drandyhaas/HaasoscopePro/adc board/Kicad/ADC.kicad_sch

## KiCad design adc board/Kicad/ADC.kicad_sch (2025-04-30)

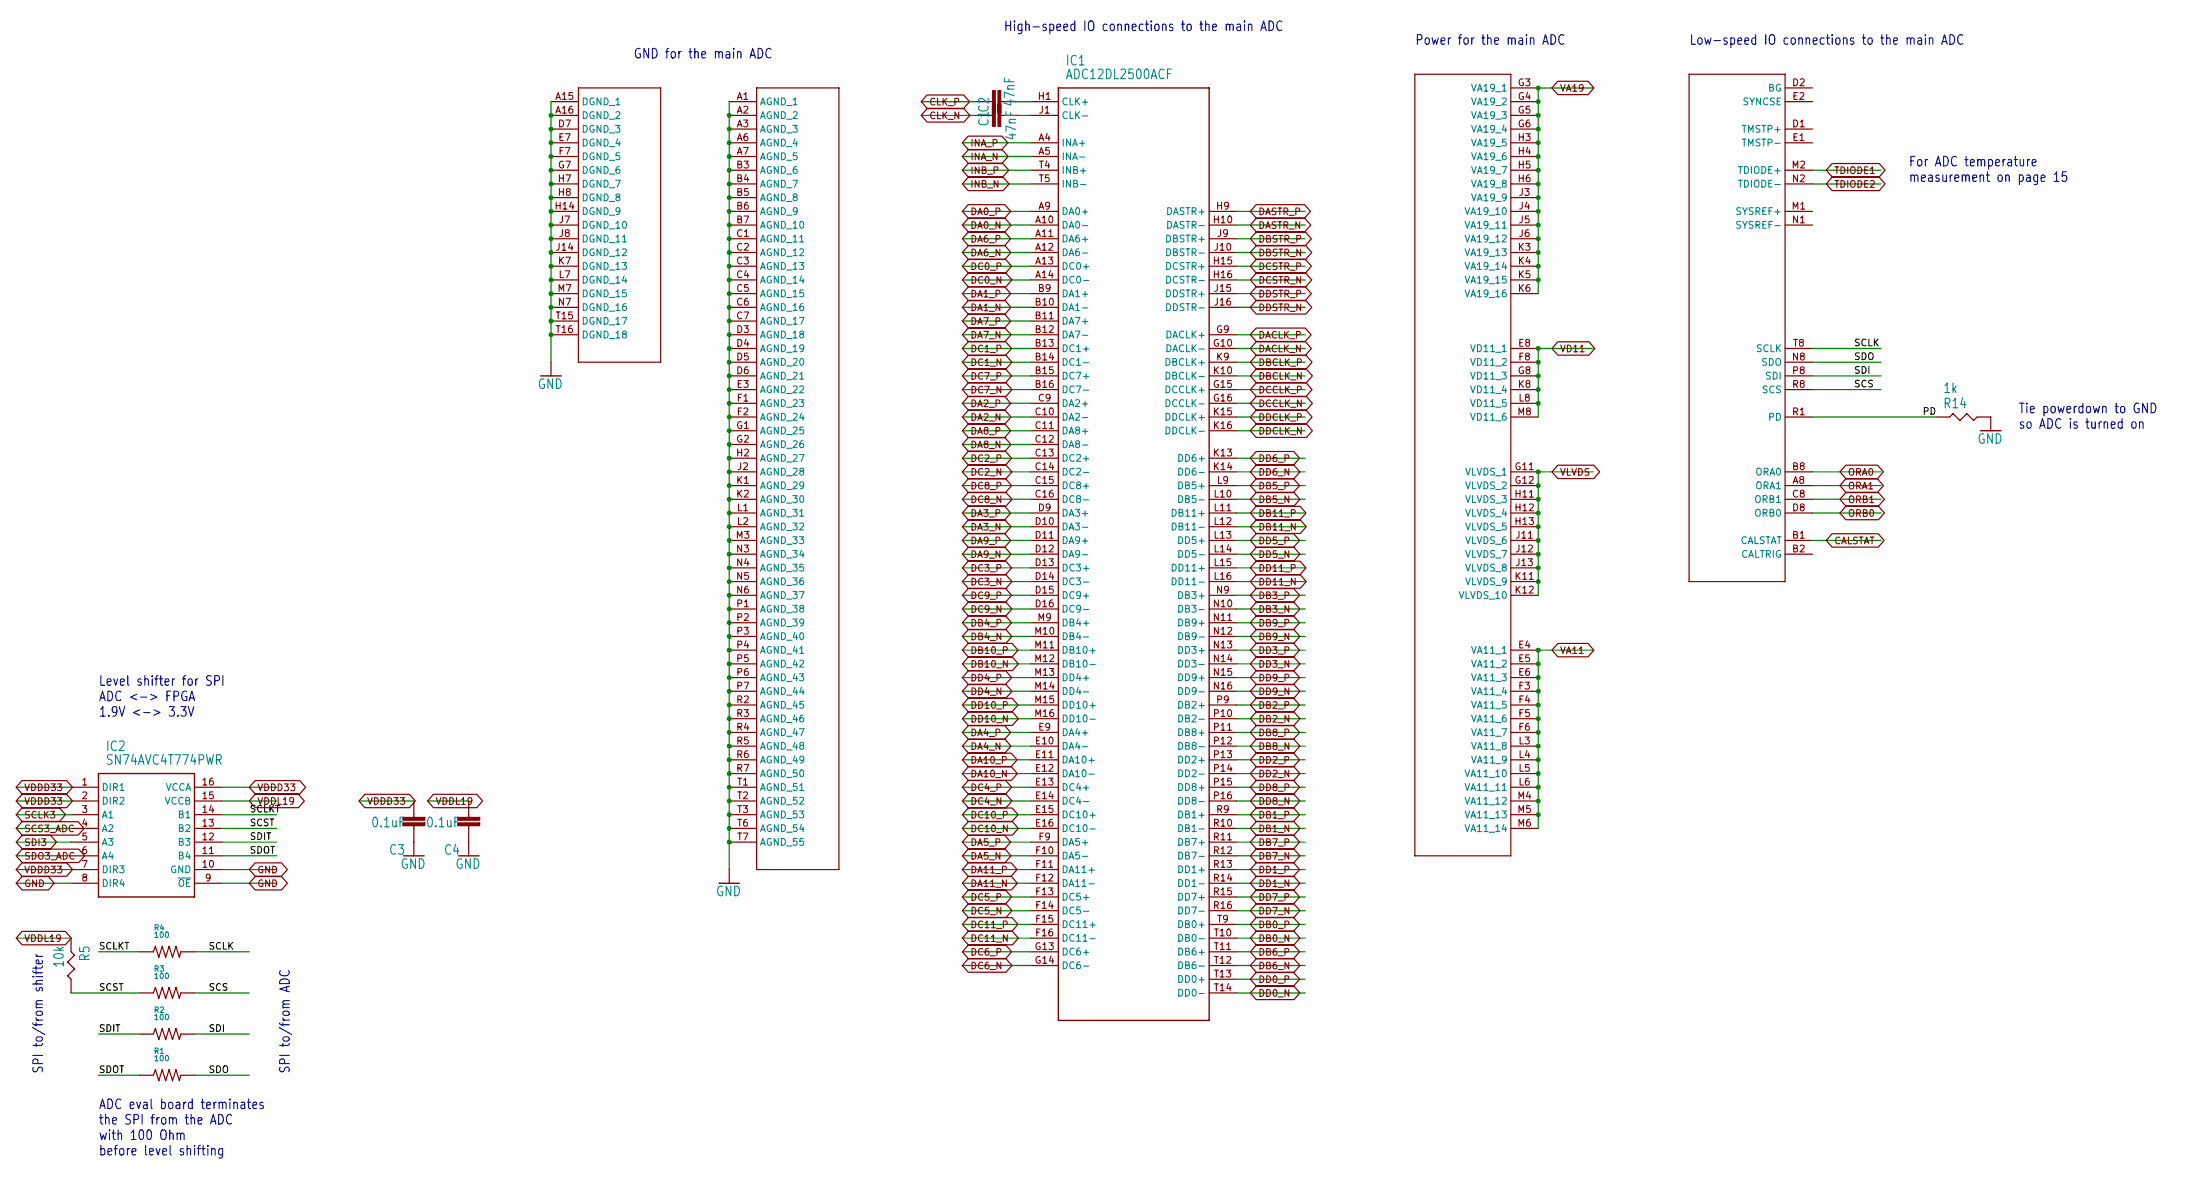
[picture p5: schematic ADC.kicad_sch]

Parts:
C1, C2: 47nF; RESC0402_N
C3, C4: 0.1uF; RESC0402_N
IC1: ADC12DL2500ACF; BGA256C100P16X16_1700X1700X331; MANUFACTURER_PART_NUMBER ADC12DL500ACF
IC2: SN74AVC4T774PWR; SOP65P640X120-16N
R1, R2, R3, R4: 100; 0201
R5: 10k; RES-0402
R14: 1k; RES-0402

Connections:
CALSTAT: IC1.B1 (CALSTAT)
CLK_N: C1.2
CLK_P: C2.1
DA0_N: IC1.A10 (DA0-)
DA0_P: IC1.A9 (DA0+)
DA1_N: IC1.B10 (DA1-)
DA1_P: IC1.B9 (DA1+)
DA2_N: IC1.C10 (DA2-)
DA2_P: IC1.C9 (DA2+)
DA3_N: IC1.D10 (DA3-)
DA3_P: IC1.D9 (DA3+)
DA4_N: IC1.E10 (DA4-)
DA4_P: IC1.E9 (DA4+)
DA5_N: IC1.F10 (DA5-)
DA5_P: IC1.F9 (DA5+)
DA6_N: IC1.A12 (DA6-)
DA6_P: IC1.A11 (DA6+)
DA7_N: IC1.B12 (DA7-)
DA7_P: IC1.B11 (DA7+)
DA8_N: IC1.C12 (DA8-)
DA8_P: IC1.C11 (DA8+)
DA9_N: IC1.D12 (DA9-)
DA9_P: IC1.D11 (DA9+)
DA10_N: IC1.E12 (DA10-)
DA10_P: IC1.E11 (DA10+)
DA11_N: IC1.F12 (DA11-)
DA11_P: IC1.F11 (DA11+)
DACLK_N: IC1.G10 (DACLK-)
DACLK_P: IC1.G9 (DACLK+)
DASTR_N: IC1.H10 (DASTR-)
DASTR_P: IC1.H9 (DASTR+)
DB0_N: IC1.T10 (DB0-)
DB0_P: IC1.T9 (DB0+)
DB1_N: IC1.R10 (DB1-)
DB1_P: IC1.R9 (DB1+)
DB2_N: IC1.P10 (DB2-)
DB2_P: IC1.P9 (DB2+)
DB3_N: IC1.N10 (DB3-)
DB3_P: IC1.N9 (DB3+)
DB4_N: IC1.M10 (DB4-)
DB4_P: IC1.M9 (DB4+)
DB5_N: IC1.L10 (DB5-)
DB5_P: IC1.L9 (DB5+)
DB6_N: IC1.T12 (DB6-)
DB6_P: IC1.T11 (DB6+)
DB7_N: IC1.R12 (DB7-)
DB7_P: IC1.R11 (DB7+)
DB8_N: IC1.P12 (DB8-)
DB8_P: IC1.P11 (DB8+)
DB9_N: IC1.N12 (DB9-)
DB9_P: IC1.N11 (DB9+)
DB10_N: IC1.M12 (DB10-)
DB10_P: IC1.M11 (DB10+)
DB11_N: IC1.L12 (DB11-)
DB11_P: IC1.L11 (DB11+)
DBCLK_N: IC1.K10 (DBCLK-)
DBCLK_P: IC1.K9 (DBCLK+)
DBSTR_N: IC1.J10 (DBSTR-)
DBSTR_P: IC1.J9 (DBSTR+)
DC0_N: IC1.A14 (DC0-)
DC0_P: IC1.A13 (DC0+)
DC1_N: IC1.B14 (DC1-)
DC1_P: IC1.B13 (DC1+)
DC2_N: IC1.C14 (DC2-)
DC2_P: IC1.C13 (DC2+)
DC3_N: IC1.D14 (DC3-)
DC3_P: IC1.D13 (DC3+)
DC4_N: IC1.E14 (DC4-)
DC4_P: IC1.E13 (DC4+)
DC5_N: IC1.F14 (DC5-)
DC5_P: IC1.F13 (DC5+)
DC6_N: IC1.G14 (DC6-)
DC6_P: IC1.G13 (DC6+)
DC7_N: IC1.B16 (DC7-)
DC7_P: IC1.B15 (DC7+)
DC8_N: IC1.C16 (DC8-)
DC8_P: IC1.C15 (DC8+)
DC9_N: IC1.D16 (DC9-)
DC9_P: IC1.D15 (DC9+)
DC10_N: IC1.E16 (DC10-)
DC10_P: IC1.E15 (DC10+)
DC11_N: IC1.F16 (DC11-)
DC11_P: IC1.F15 (DC11+)
DCCLK_N: IC1.G16 (DCCLK-)
DCCLK_P: IC1.G15 (DCCLK+)
DCSTR_N: IC1.H16 (DCSTR-)
DCSTR_P: IC1.H15 (DCSTR+)
DD0_N: IC1.T14 (DD0-)
DD0_P: IC1.T13 (DD0+)
DD1_N: IC1.R14 (DD1-)
DD1_P: IC1.R13 (DD1+)
DD2_N: IC1.P14 (DD2-)
DD2_P: IC1.P13 (DD2+)
DD3_N: IC1.N14 (DD3-)
DD3_P: IC1.N13 (DD3+)
DD4_N: IC1.M14 (DD4-)
DD4_P: IC1.M13 (DD4+)
DD5_N: IC1.L14 (DD5-)
DD5_P: IC1.L13 (DD5+)
DD6_N: IC1.K14 (DD6-)
DD6_P: IC1.K13 (DD6+)
DD7_N: IC1.R16 (DD7-)
DD7_P: IC1.R15 (DD7+)
DD8_N: IC1.P16 (DD8-)
DD8_P: IC1.P15 (DD8+)
DD9_N: IC1.N16 (DD9-)
DD9_P: IC1.N15 (DD9+)
DD10_N: IC1.M16 (DD10-)
DD10_P: IC1.M15 (DD10+)
DD11_N: IC1.L16 (DD11-)
DD11_P: IC1.L15 (DD11+)
DDCLK_N: IC1.K16 (DDCLK-)
DDCLK_P: IC1.K15 (DDCLK+)
DDSTR_N: IC1.J16 (DDSTR-)
DDSTR_P: IC1.J15 (DDSTR+)
GND: C3.1, C4.1, IC1.A1 (AGND_1), IC1.A2 (AGND_2), IC1.A3 (AGND_3), IC1.A6 (AGND_4), IC1.A7 (AGND_5), IC1.A15 (DGND_1), IC1.A16 (DGND_2), IC1.B3 (AGND_6), IC1.B4 (AGND_7), IC1.B5 (AGND_8), IC1.B6 (AGND_9), IC1.B7 (AGND_10), IC1.C1 (AGND_11), IC1.C2 (AGND_12), IC1.C3 (AGND_13), IC1.C4 (AGND_14), IC1.C5 (AGND_15), IC1.C6 (AGND_16), IC1.C7 (AGND_17), IC1.D3 (AGND_18), IC1.D4 (AGND_19), IC1.D5 (AGND_20), IC1.D6 (AGND_21), IC1.D7 (DGND_3), IC1.E3 (AGND_22), IC1.E7 (DGND_4), IC1.F1 (AGND_23), IC1.F2 (AGND_24), IC1.F7 (DGND_5), IC1.G1 (AGND_25), IC1.G2 (AGND_26), IC1.G7 (DGND_6), IC1.H2 (AGND_27), IC1.H7 (DGND_7), IC1.H8 (DGND_8), IC1.H14 (DGND_9), IC1.J2 (AGND_28), IC1.J7 (DGND_10), IC1.J8 (DGND_11), IC1.J14 (DGND_12), IC1.K1 (AGND_29), IC1.K2 (AGND_30), IC1.K7 (DGND_13), IC1.L1 (AGND_31), IC1.L2 (AGND_32), IC1.L7 (DGND_14), IC1.M3 (AGND_33), IC1.M7 (DGND_15), IC1.N3 (AGND_34), IC1.N4 (AGND_35), IC1.N5 (AGND_36), IC1.N6 (AGND_37), IC1.N7 (DGND_16), IC1.P1 (AGND_38), IC1.P2 (AGND_39), IC1.P3 (AGND_40), IC1.P4 (AGND_41), IC1.P5 (AGND_42), IC1.P6 (AGND_43), IC1.P7 (AGND_44), IC1.R2 (AGND_45), IC1.R3 (AGND_46), IC1.R4 (AGND_47), IC1.R5 (AGND_48), IC1.R6 (AGND_49), IC1.R7 (AGND_50), IC1.T1 (AGND_51), IC1.T2 (AGND_52), IC1.T3 (AGND_53), IC1.T6 (AGND_54), IC1.T7 (AGND_55), IC1.T15 (DGND_17), IC1.T16 (DGND_18), IC2.8 (DIR4), IC2.9 (~OE), IC2.10 (GND), R14.P$2
INA_N: IC1.A5 (INA-)
INA_P: IC1.A4 (INA+)
INB_N: IC1.T5 (INB-)
INB_P: IC1.T4 (INB+)
unnamed: C1.1, IC1.J1 (CLK-)
unnamed: C2.2, IC1.H1 (CLK+)
ORA0: IC1.B8 (ORA0)
ORA1: IC1.A8 (ORA1)
ORB0: IC1.D8 (ORB0)
ORB1: IC1.C8 (ORB1)
PD: IC1.R1 (PD), R14.P$1
SCLK: IC1.T8 (SCLK), R4.2
SCLK3: IC2.3 (A1)
SCLKT: IC2.14 (B1), R4.1
SCS: IC1.R8 (SCS), R3.2
SCS3_ADC: IC2.4 (A2)
SCST: IC2.13 (B2), R3.1, R5.P$2
SDI: IC1.P8 (SDI), R2.2
SDI3: IC2.5 (A3)
SDIT: IC2.12 (B3), R2.1
SDO: IC1.N8 (SDO), R1.2
SDO3_ADC: IC2.6 (A4)
SDOT: IC2.11 (B4), R1.1
TDIODE1: IC1.M2 (TDIODE+)
TDIODE2: IC1.N2 (TDIODE-)
VA11: IC1.E4 (VA11_1), IC1.E5 (VA11_2), IC1.E6 (VA11_3), IC1.F3 (VA11_4), IC1.F4 (VA11_5), IC1.F5 (VA11_6), IC1.F6 (VA11_7), IC1.L3 (VA11_8), IC1.L4 (VA11_9), IC1.L5 (VA11_10), IC1.L6 (VA11_11), IC1.M4 (VA11_12), IC1.M5 (VA11_13), IC1.M6 (VA11_14)
VA19: IC1.G3 (VA19_1), IC1.G4 (VA19_2), IC1.G5 (VA19_3), IC1.G6 (VA19_4), IC1.H3 (VA19_5), IC1.H4 (VA19_6), IC1.H5 (VA19_7), IC1.H6 (VA19_8), IC1.J3 (VA19_9), IC1.J4 (VA19_10), IC1.J5 (VA19_11), IC1.J6 (VA19_12), IC1.K3 (VA19_13), IC1.K4 (VA19_14), IC1.K5 (VA19_15), IC1.K6 (VA19_16)
VD11: IC1.E8 (VD11_1), IC1.F8 (VD11_2), IC1.G8 (VD11_3), IC1.K8 (VD11_4), IC1.L8 (VD11_5), IC1.M8 (VD11_6)
VDDD33: C3.2, IC2.1 (DIR1), IC2.2 (DIR2), IC2.7 (DIR3), IC2.16 (VCCA)
VDDL19: C4.2, IC2.15 (VCCB), R5.P$1
VLVDS: IC1.G11 (VLVDS_1), IC1.G12 (VLVDS_2), IC1.H11 (VLVDS_3), IC1.H12 (VLVDS_4), IC1.H13 (VLVDS_5), IC1.J11 (VLVDS_6), IC1.J12 (VLVDS_7), IC1.J13 (VLVDS_8), IC1.K11 (VLVDS_9), IC1.K12 (VLVDS_10)

Notes on the sheet:
Tie powerdown to GND so ADC is turned on
ADC eval board terminates the SPI from the ADC with 100 Ohm before level shifting
High-speed IO connections to the main ADC
For ADC temperature measurement on page 15
SPI to/from shifter
Level shifter for SPI ADC <-> FPGA 1.9V <-> 3.3V
GND for the main ADC
SPI to/from ADC
Power for the main ADC
Low-speed IO connections to the main ADC
