drandyhaas/HaasoscopePro/adc board/Kicad/Clock.kicad_sch

## KiCad design adc board/Kicad/Clock.kicad_sch (2025-04-30)

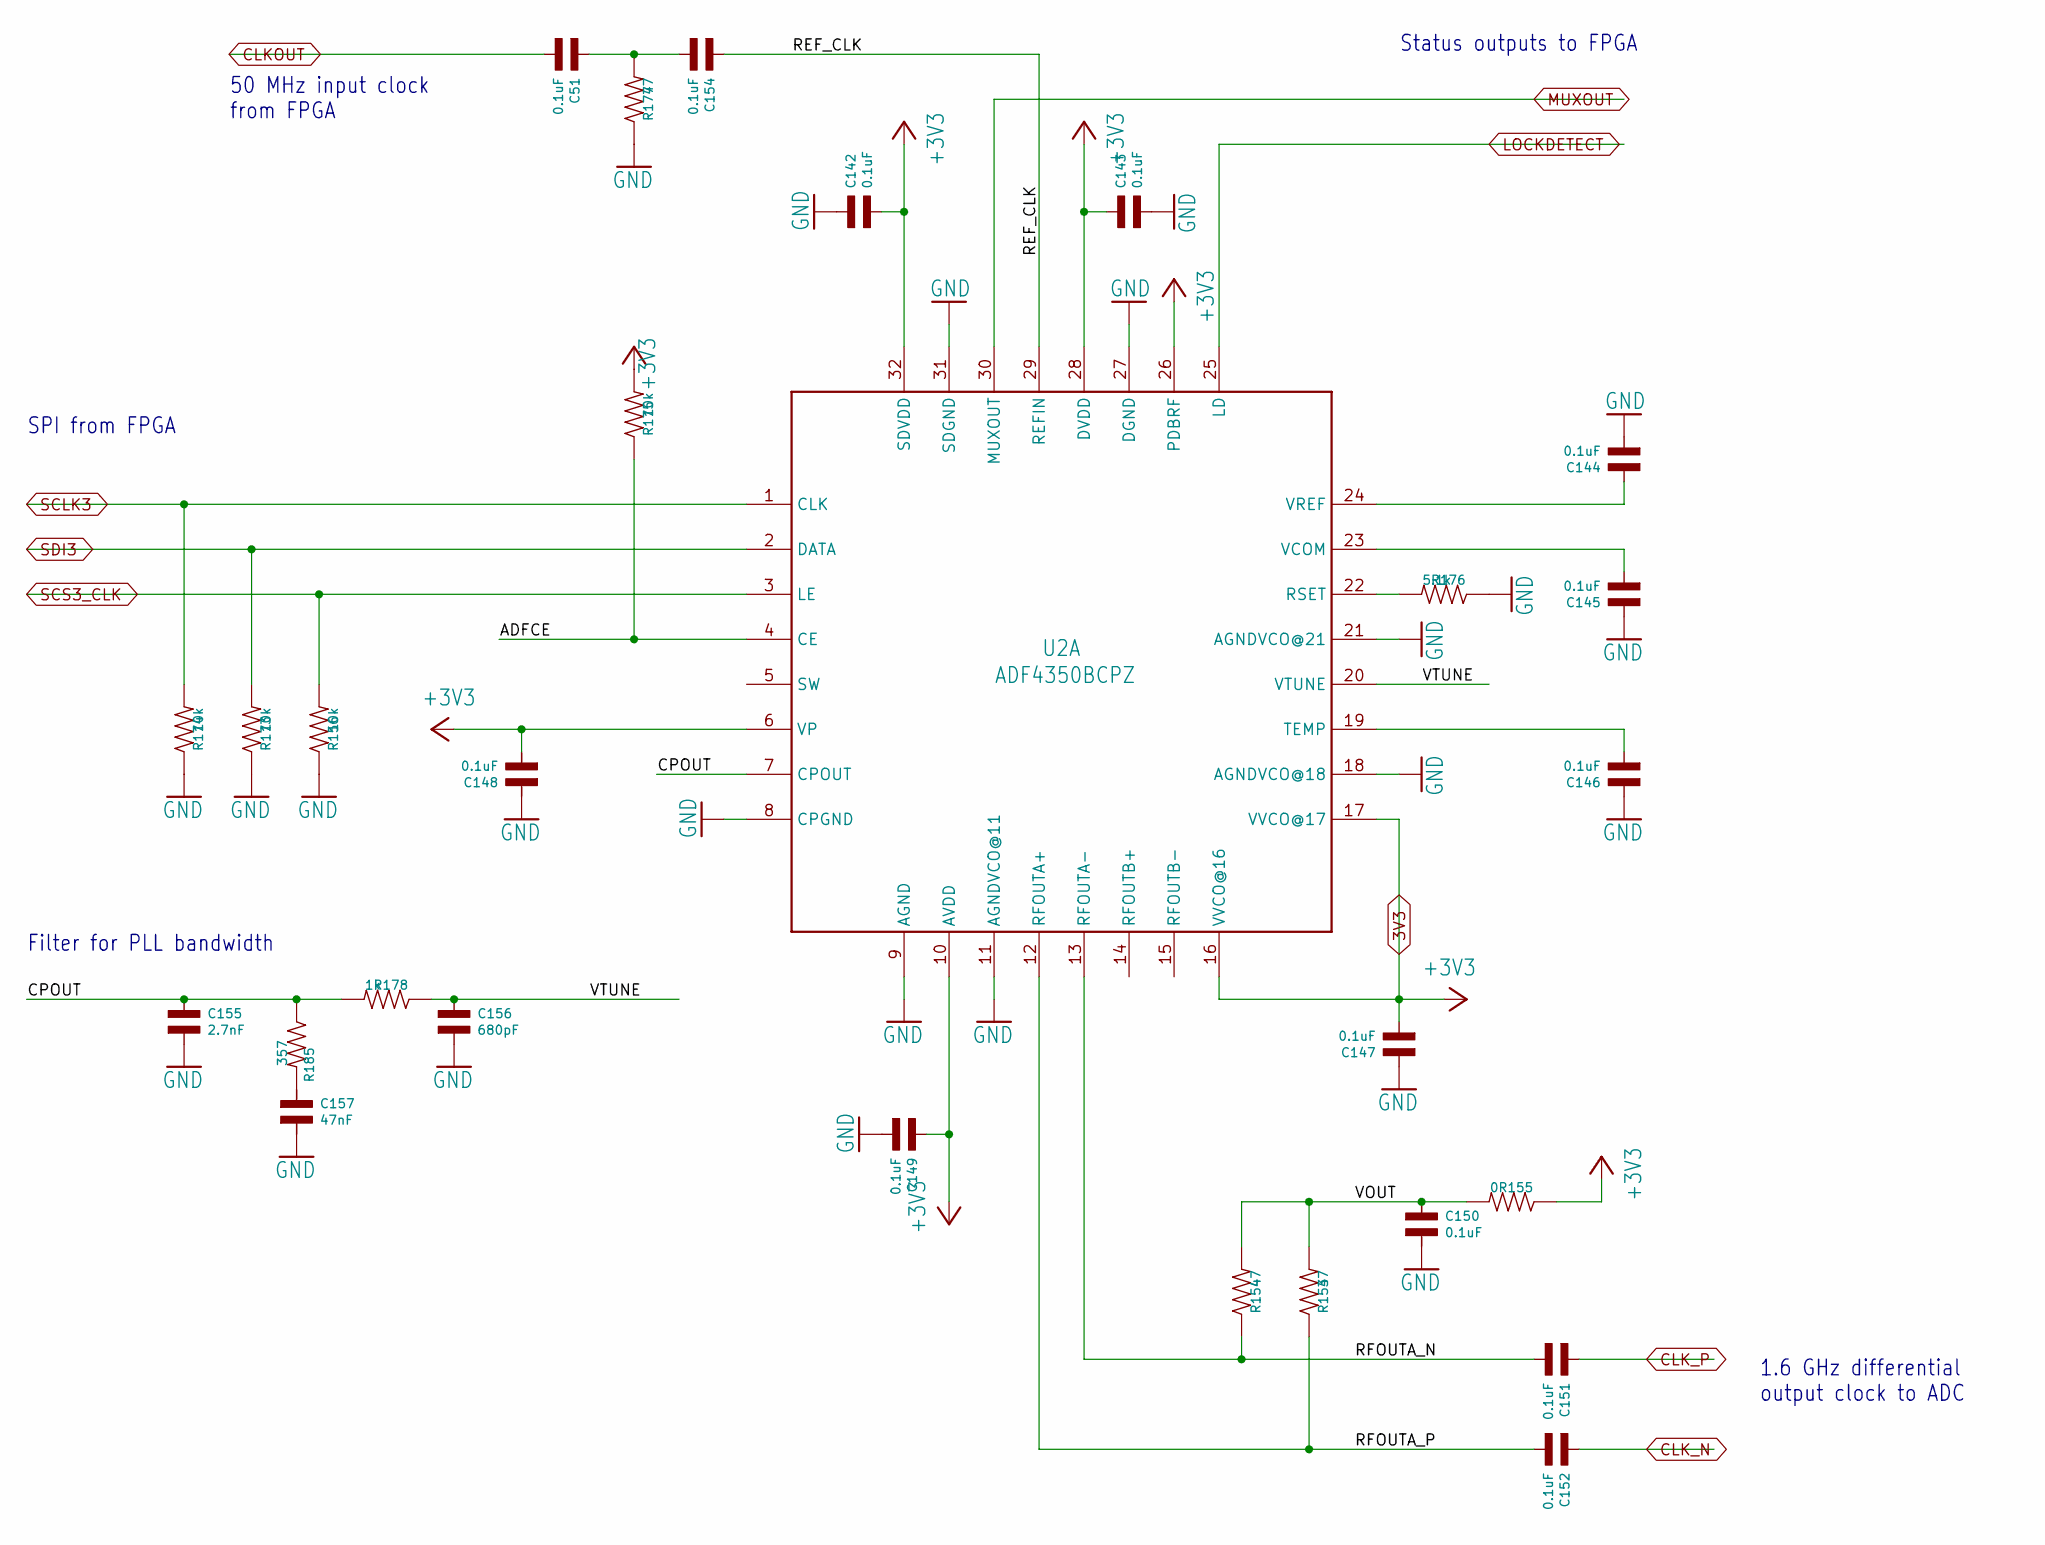
[picture p6: schematic Clock.kicad_sch]

Parts:
C51, C142, C143, C144, C145, C146, C147, C148, C149, C150, C151, C152, C154: 0.1uF; C0402
C155: 2.7nF; C0402
C156: 680pF; C0402
C157: 47nF; C0402
R153, R154, R177: 47; R0402
R155: 0; R0402
R156, R173, R174, R175: 10k; R0402
R176: 5.1k; R0402
R178: 1k; R0402
R185: 357; R0402
U2: ADF4350BCPZ; QFN50P500X500X100-33V2N

Connections:
+3V3: C142.P$2, C143.P$1, C147.P$2, C148.P$2, C149.P$1, R155.P$1, R175.P$2, U2.6 (VP), U2.10 (AVDD), U2.16 (VVCO@16), U2.17 (VVCO@17), U2.26 (PDBRF), U2.28 (DVDD), U2.32 (SDVDD)
ADFCE: R175.P$1, U2.4 (CE)
CLKOUT: C51.P$2
CLK_N: C152.P$1
CLK_P: C151.P$1
CPOUT: C155.P$1, R178.P$2, R185.P$1, U2.7 (CPOUT)
GND: C142.P$1, C143.P$2, C144.P$2, C145.P$1, C146.P$1, C147.P$1, C148.P$1, C149.P$2, C150.P$2, C155.P$2, C156.P$2, C157.P$2, R156.P$1, R173.P$1, R174.P$1, R176.P$1, R177.P$1, U2.8 (CPGND), U2.9 (AGND), U2.11 (AGNDVCO@11), U2.18 (AGNDVCO@18), U2.21 (AGNDVCO@21), U2.27 (DGND), U2.31 (SDGND)
LOCKDETECT: U2.25 (LD)
MUXOUT: U2.30 (MUXOUT)
unnamed: C144.P$1, U2.24 (VREF)
unnamed: C145.P$2, U2.23 (VCOM)
unnamed: C146.P$2, U2.19 (TEMP)
unnamed: C51.P$1, C154.P$2, R177.P$2
unnamed: C157.P$1, R185.P$2
unnamed: R176.P$2, U2.22 (RSET)
REF_CLK: C154.P$1, U2.29 (REFIN)
RFOUTA_N: C151.P$2, R154.P$1, U2.13 (RFOUTA-)
RFOUTA_P: C152.P$2, R153.P$1, U2.12 (RFOUTA+)
SCLK3: R174.P$2, U2.1 (CLK)
SCS3_CLK: R156.P$2, U2.3 (LE)
SDI3: R173.P$2, U2.2 (DATA)
VOUT: C150.P$1, R153.P$2, R154.P$2, R155.P$2
VTUNE: C156.P$1, R178.P$1, U2.20 (VTUNE)

Notes on the sheet:
Status outputs to FPGA
50 MHz input clock from FPGA
1.6 GHz differential output clock to ADC
SPI from FPGA
Filter for PLL bandwidth
