drandyhaas/HaasoscopePro/adc board/Kicad/Data_output.kicad_sch

## KiCad design adc board/Kicad/Data_output.kicad_sch (2025-04-30)

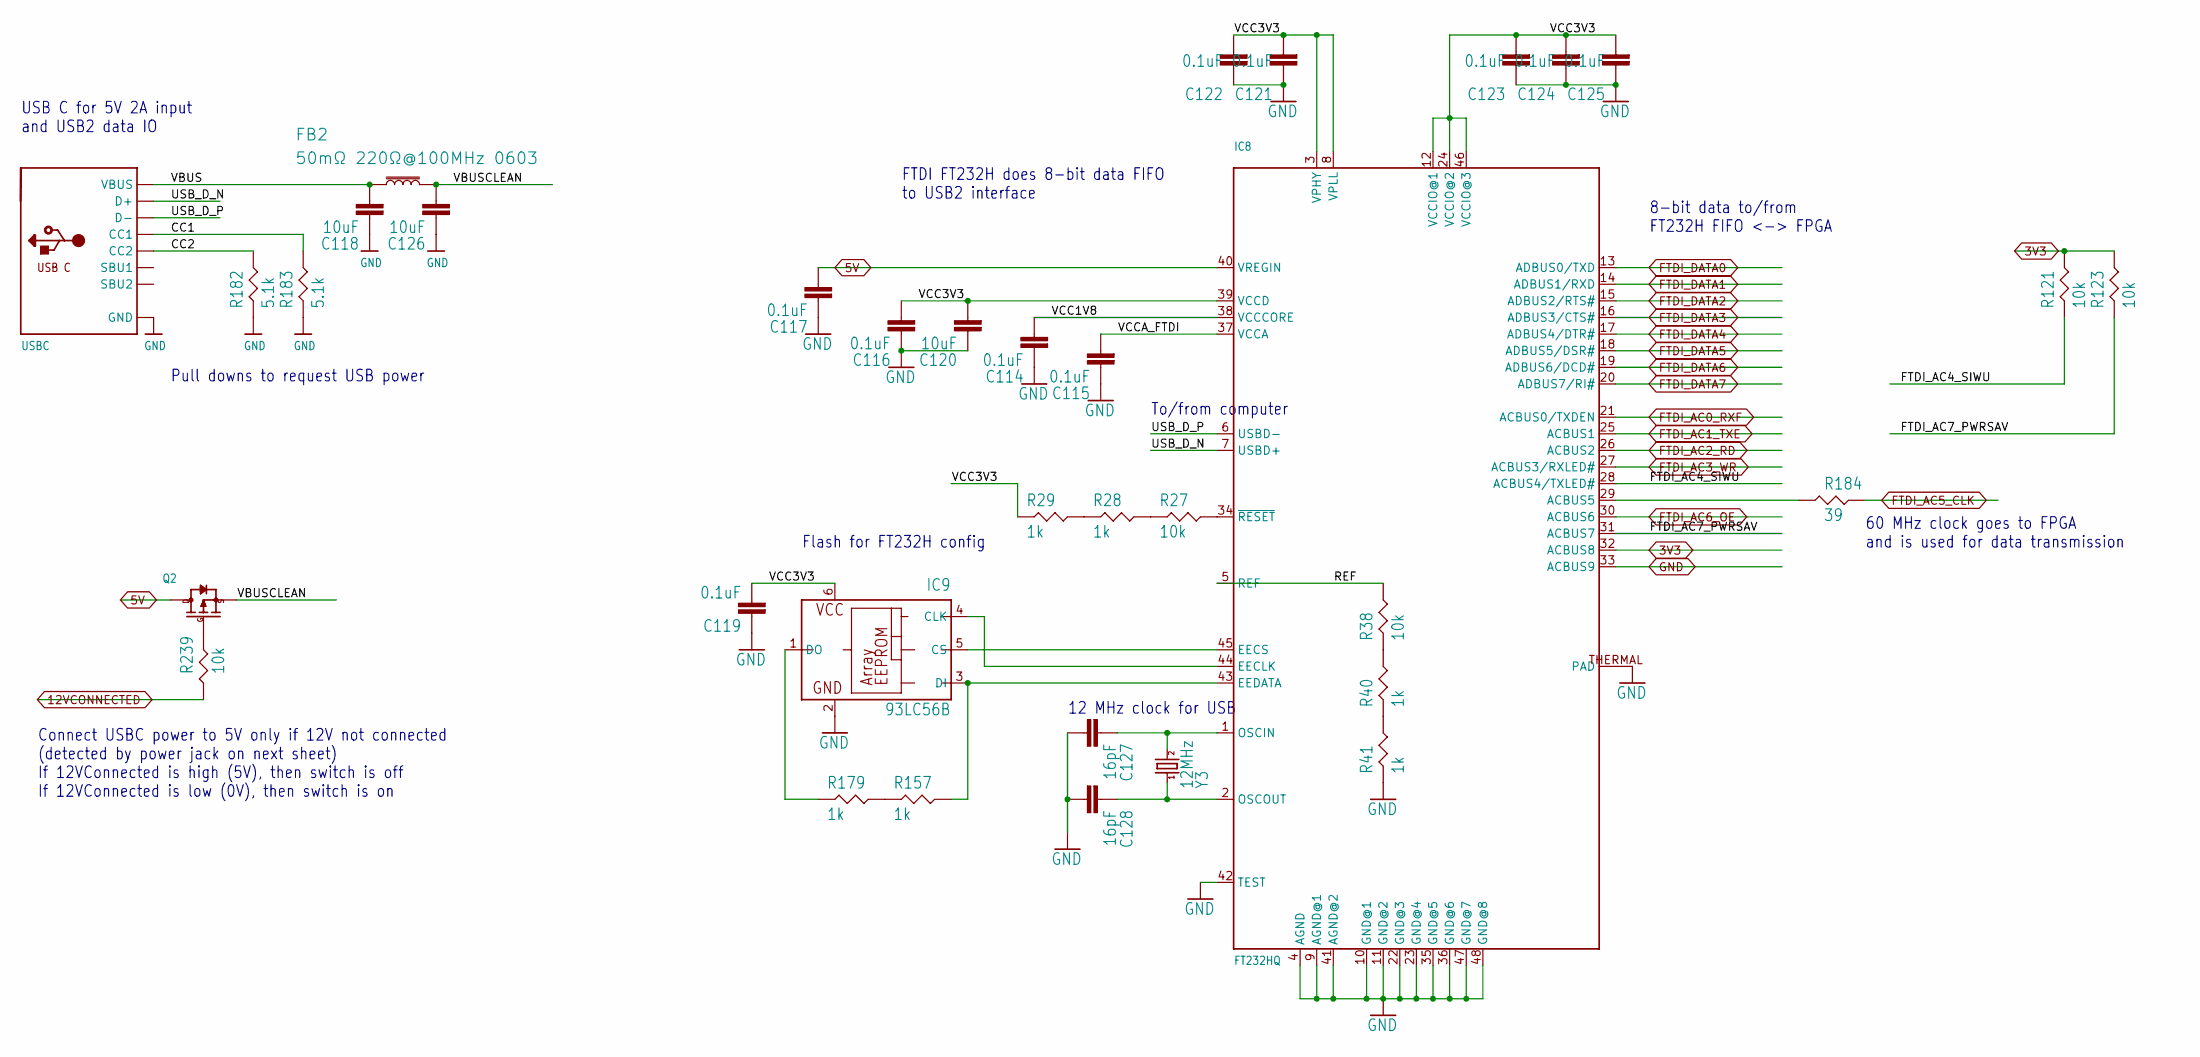
[picture p7: schematic Data_output.kicad_sch]

Parts:
C114, C115, C116, C117, C119, C121, C122, C123, C124, C125: 0.1uF; RESC0402_N
C118, C120, C126: 10uF; RESC0805_N
C127, C128: 16pF; RESC0402_N
FB2: 50mΩ 220Ω@100MHz 0603; 0603
IC8: FT232HQ; QFN48_8MM; JLC_ROTATION 270
IC9: 93LC56B; SOT23-6
Q2: FDN340P; SOT-23; MPN P-MOS AO3401A
R27, R38, R121, R123, R239: 10k; RES-0402
R28, R29, R40, R41, R157, R179: 1k; RES-0402
R182, R183: 5.1k; RES-0402
R184: 39; RES-0402
X1: USBC; USB_C_CUSB31-CFM2AX-01-X
Y3: 12MHz; CRYSTAL-SMD-5X3; LCSC C2901628

Connections:
3V3: IC8.32 (ACBUS8), R121.P$2, R123.P$2
5V: C117.2, IC8.40 (VREGIN), Q2.3 (D)
12VCONNECTED: R239.P$1
CC1: R183.P$2, X1.A5 (CC1)
CC2: R182.P$2, X1.B5 (CC2)
FTDI_AC0_RXF: IC8.21 (ACBUS0/TXDEN)
FTDI_AC1_TXE: IC8.25 (ACBUS1)
FTDI_AC2_RD: IC8.26 (ACBUS2)
FTDI_AC3_WR: IC8.27 (ACBUS3/RXLED#)
FTDI_AC4_SIWU: IC8.28 (ACBUS4/TXLED#), R121.P$1
FTDI_AC5_CLK: R184.P$2
FTDI_AC6_OE: IC8.30 (ACBUS6)
FTDI_AC7_PWRSAV: IC8.31 (ACBUS7), R123.P$1
FTDI_DATA0: IC8.13 (ADBUS0/TXD)
FTDI_DATA1: IC8.14 (ADBUS1/RXD)
FTDI_DATA2: IC8.15 (ADBUS2/RTS#)
FTDI_DATA3: IC8.16 (ADBUS3/CTS#)
FTDI_DATA4: IC8.17 (ADBUS4/DTR#)
FTDI_DATA5: IC8.18 (ADBUS5/DSR#)
FTDI_DATA6: IC8.19 (ADBUS6/DCD#)
FTDI_DATA7: IC8.20 (ADBUS7/RI#)
GND: C114.1, C115.1, C116.1, C117.1, C118.1, C119.1, C120.1, C121.1, C122.1, C123.1, C124.1, C125.1, C126.1, C127.2, C128.2, IC8.4 (AGND), IC8.9 (AGND@1), IC8.10 (GND@1), IC8.11 (GND@2), IC8.22 (GND@3), IC8.23 (GND@4), IC8.33 (ACBUS9), IC8.35 (GND@5), IC8.36 (GND@6), IC8.41 (AGND@2), IC8.42 (TEST), IC8.47 (GND@7), IC8.48 (GND@8), IC8.THERMAL (PAD), IC9.2 (GND), R41.P$1, R182.P$1, R183.P$1, X1.A1B12 (GND), X1.B1A12 (GND)
unnamed: C127.1, IC8.1 (OSCIN), Y3.3 (2)
unnamed: C128.1, IC8.2 (OSCOUT), Y3.1
unnamed: IC8.29 (ACBUS5), R184.P$1
unnamed: IC8.34 (~RESET), R27.P$2
unnamed: IC8.43 (EEDATA), IC9.3 (DI), R157.P$2
unnamed: IC8.44 (EECLK), IC9.4 (CLK)
unnamed: IC8.45 (EECS), IC9.5 (CS)
unnamed: IC9.1 (DO), R179.P$1
unnamed: Q2.1 (G), R239.P$2
unnamed: R27.P$1, R28.P$2
unnamed: R28.P$1, R29.P$2
unnamed: R38.P$1, R40.P$2
unnamed: R40.P$1, R41.P$2
unnamed: R157.P$1, R179.P$2
REF: IC8.5 (REF), R38.P$2
USB_D_N: IC8.7 (USBD+), X1.A6 (D+), X1.B6 (D+)
USB_D_P: IC8.6 (USBD-), X1.A7 (D-), X1.B7 (D-)
VBUS: C118.2, FB2.1, X1.A4B9 (VBUS), X1.B4A9 (VBUS)
VBUSCLEAN: C126.2, FB2.2, Q2.2 (S)
VCC1V8: C114.2, IC8.38 (VCCCORE)
VCC3V3: C116.2, C119.2, C120.2, C121.2, C122.2, C123.2, C124.2, C125.2, IC8.3 (VPHY), IC8.8 (VPLL), IC8.12 (VCCIO@1), IC8.24 (VCCIO@2), IC8.39 (VCCD), IC8.46 (VCCIO@3), IC9.6 (VCC), R29.P$1
VCCA_FTDI: C115.2, IC8.37 (VCCA)

Notes on the sheet:
Flash for FT232H config
FTDI FT232H does 8-bit data FIFO to USB2 interface
To/from computer
Connect USBC power to 5V only if 12V not connected (detected by power jack on next sheet) If 12VConnected is high (5V), then switch is off If 12VConnected is low (0V), then switch is on
Pull downs to request USB power
12 MHz clock for USB
USB C for 5V 2A input and USB2 data IO
60 MHz clock goes to FPGA and is used for data transmission
8-bit data to/from FT232H FIFO <-> FPGA
