drandyhaas/HaasoscopePro/adc board/Kicad/FPGA_and_IOs.kicad_sch

## KiCad design adc board/Kicad/FPGA_and_IOs.kicad_sch (2025-04-30)

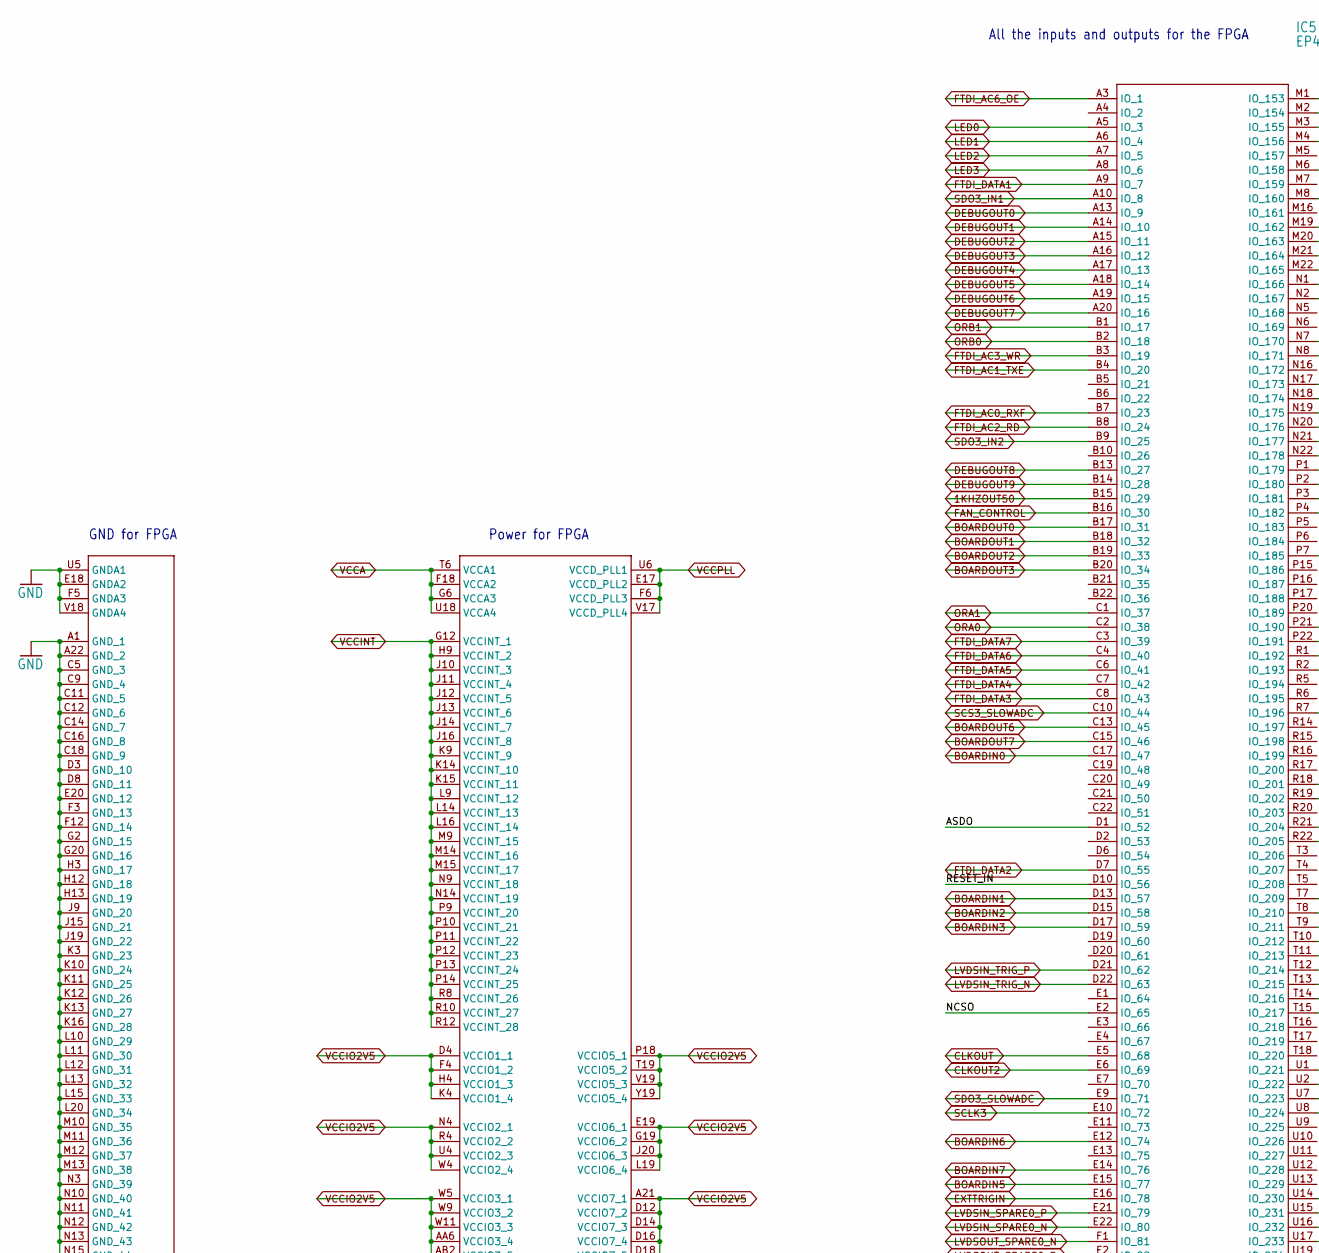
[picture p8: schematic FPGA_and_IOs.kicad_sch, part in row 1, column 1]

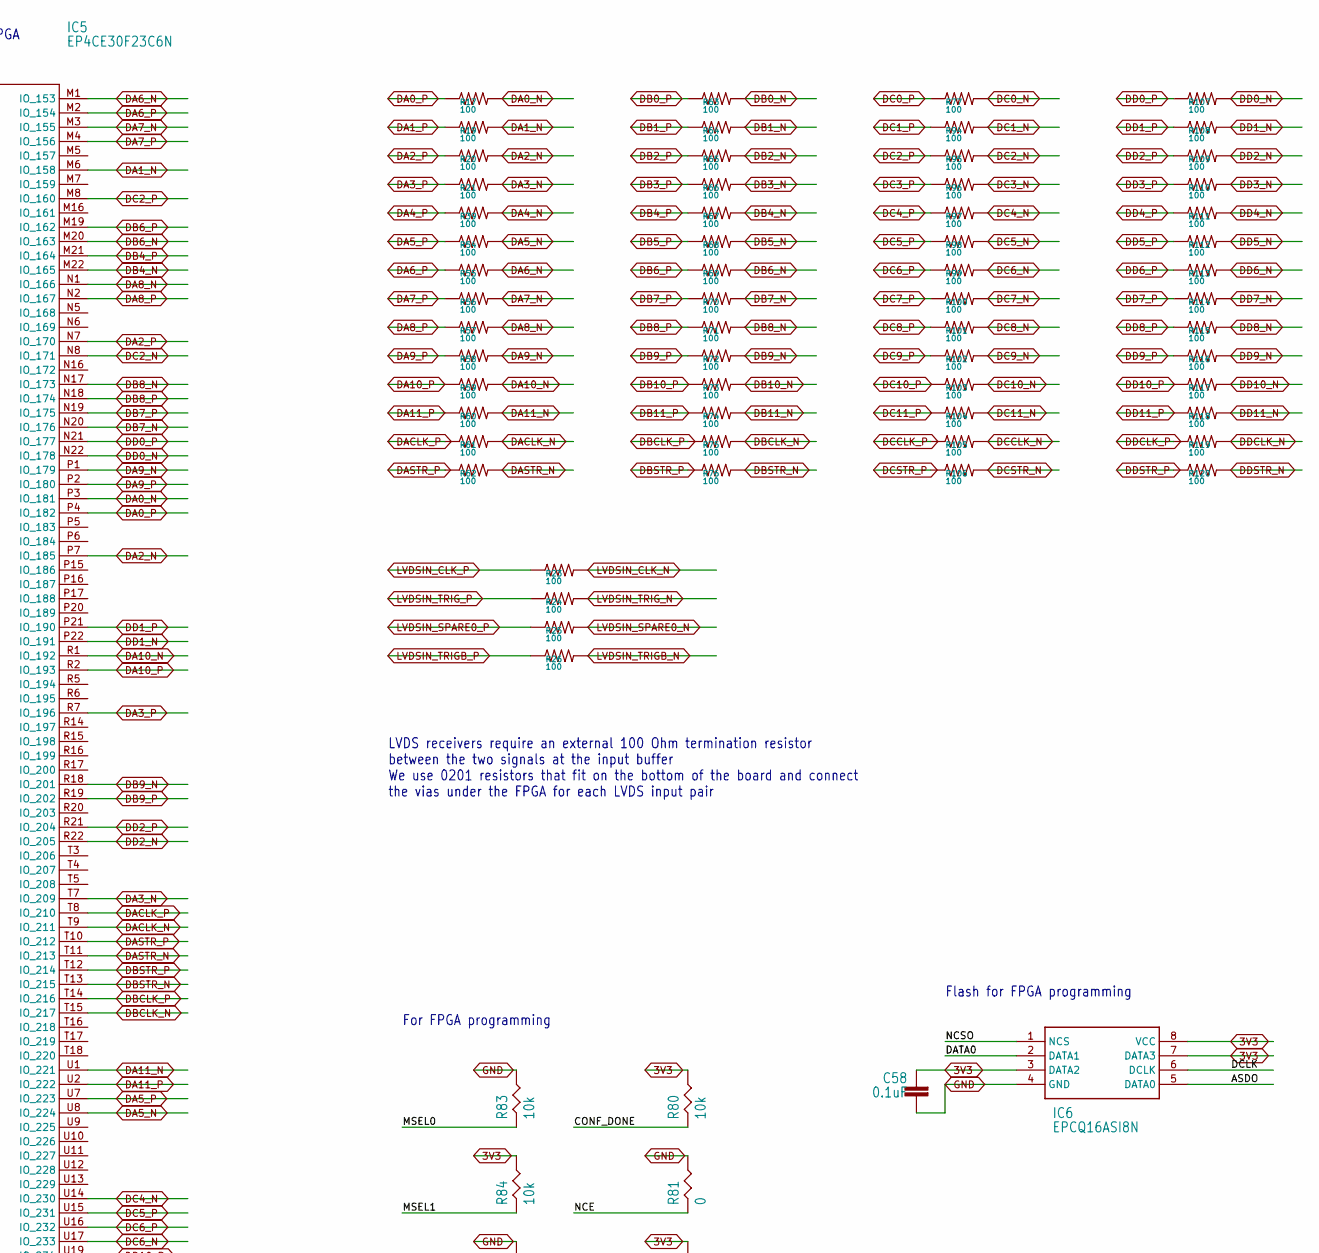
[picture p9: schematic FPGA_and_IOs.kicad_sch, part in row 1, column 2]

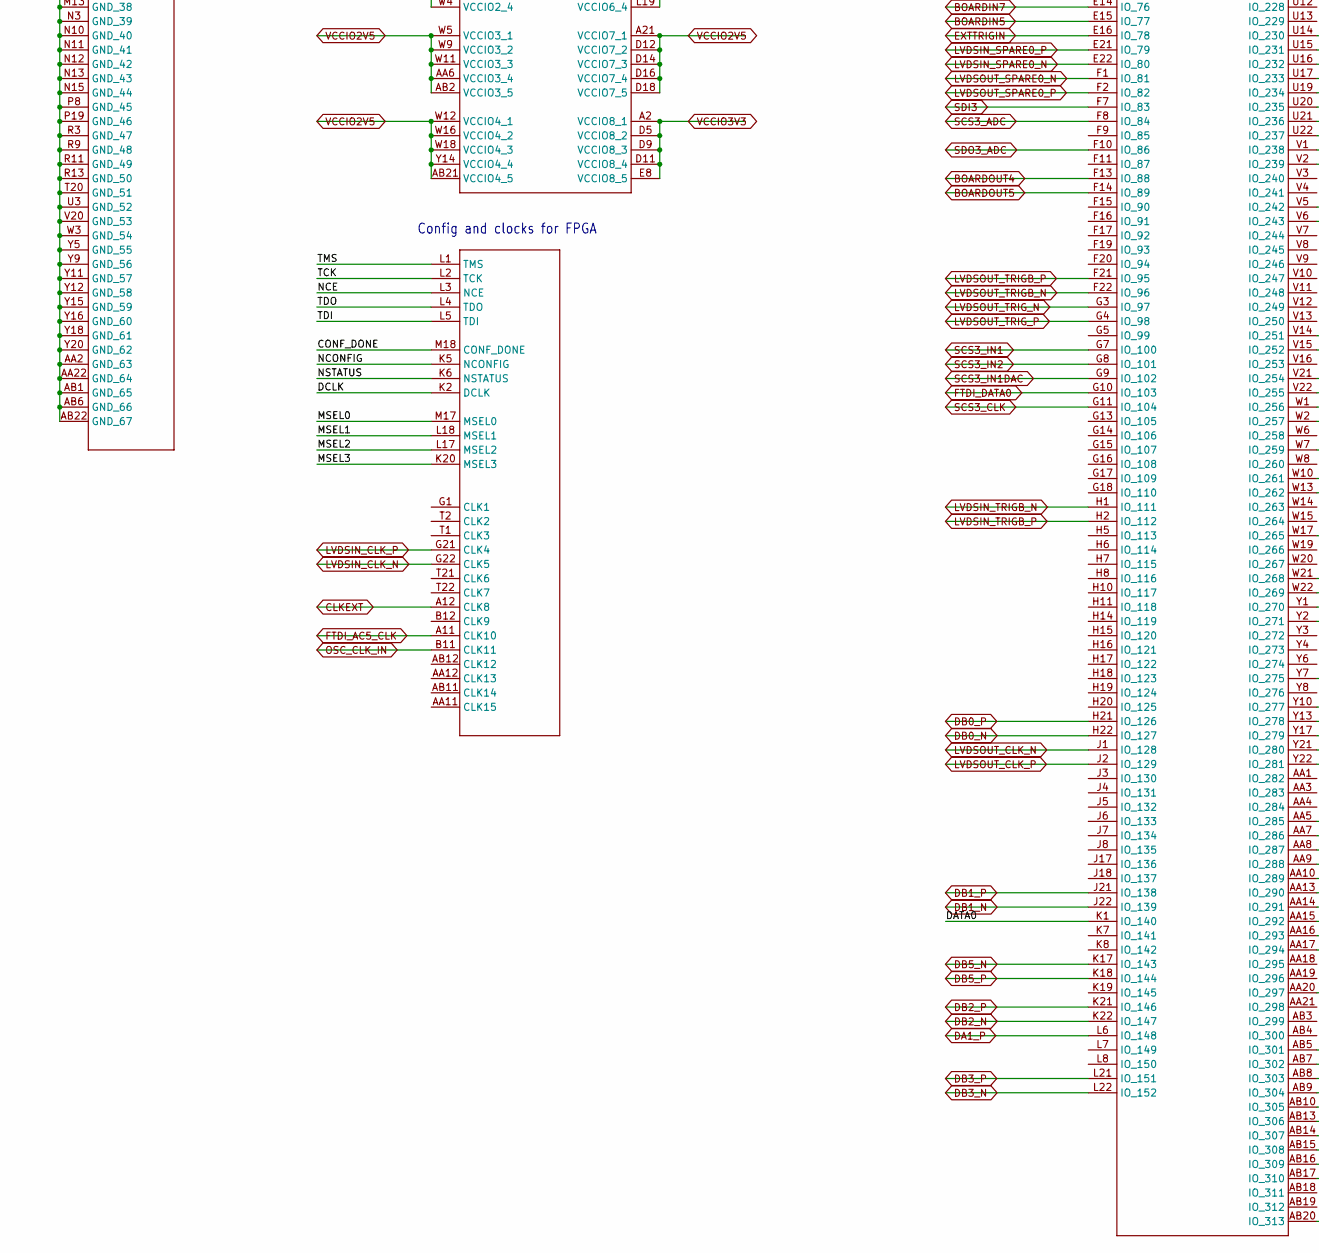
[picture p10: schematic FPGA_and_IOs.kicad_sch, part in row 2, column 1]

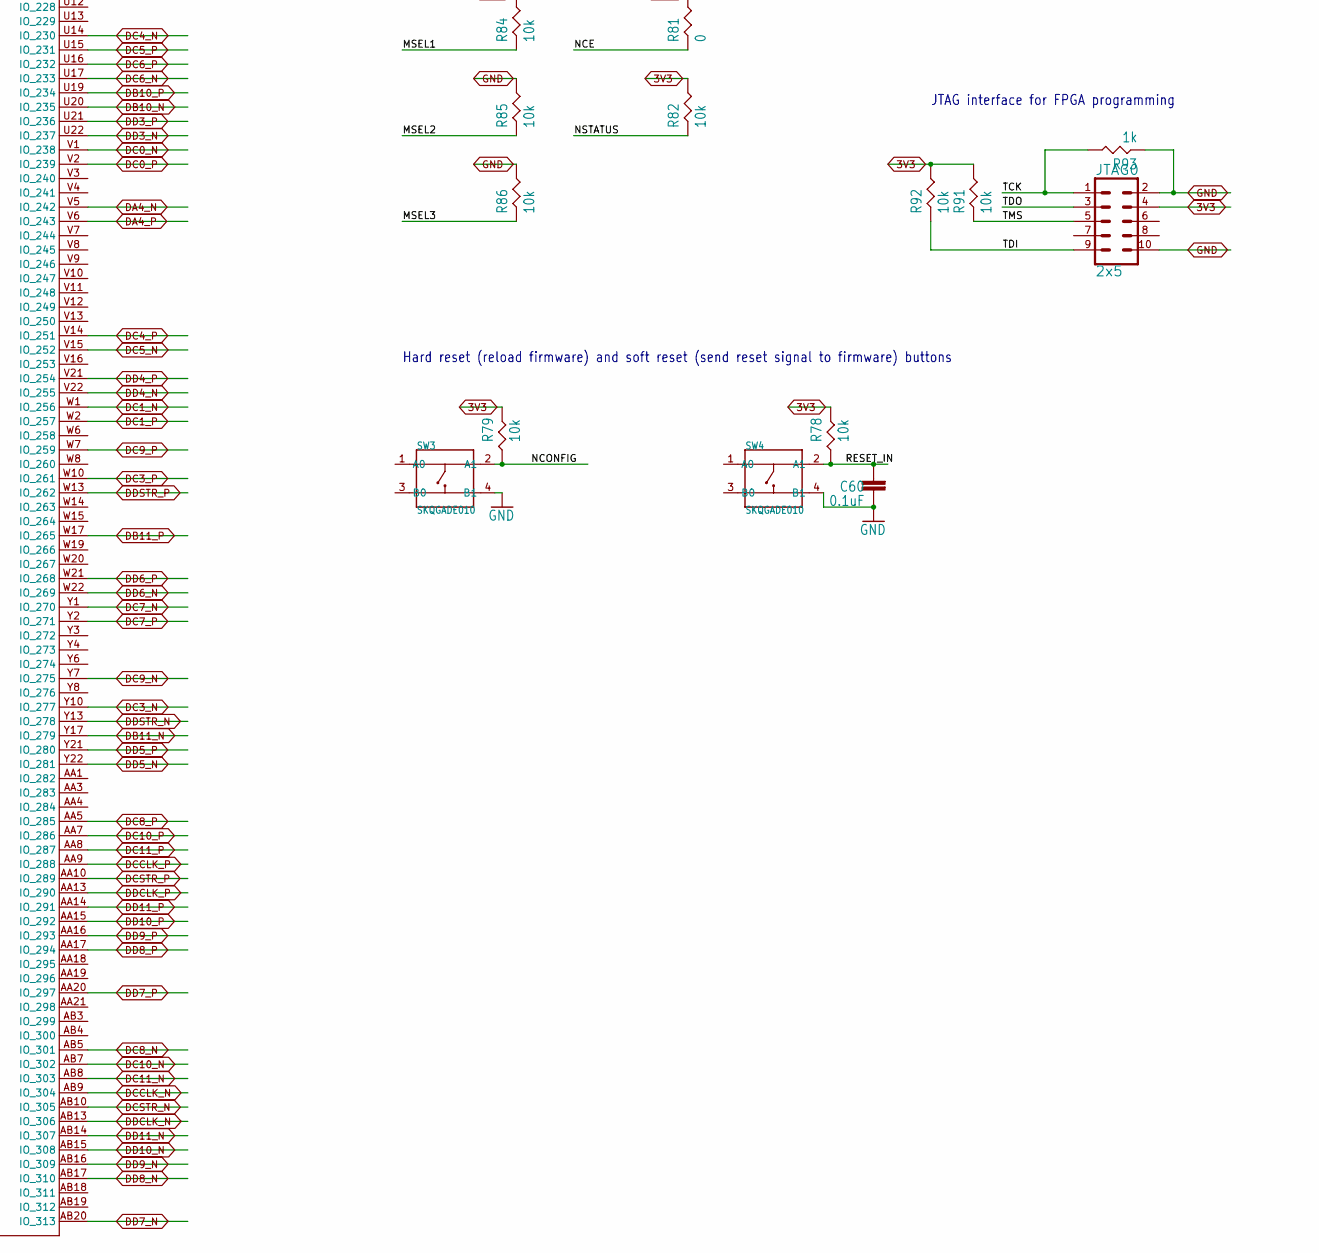
[picture p11: schematic FPGA_and_IOs.kicad_sch, part in row 2, column 2]

Parts:
C58, C60: 0.1uF; RESC0402_N
IC5: EP4CE30F23C6N; BGA484C100P22X22_2300X2300X240
IC6: EPCQ16ASI8N; SOIC127P600X175-8N
JTAG0: 2x5; 2X5-SHROUDED
R17, R19, R20, R21, R23, R24, R25, R26, R39, R54, R55, R56, R57, R58, R59, R60, R61, R62, R63, R64, R65, R66, R67, R68, R69, R70, R71, R72, R73, R74, R75, R76, R77, R94, R95, R96, R97, R98, R99, R100, R101, R102, R103, R104, R105, R106, R107, R108, R109, R110, R111, R112, R113, R114, R115, R116, R117, R118, R119, R120: 100; 0201
R78, R79, R80, R82, R83, R84, R85, R86, R91, R92: 10k; RES-0402
R81: 0; RES-0402
R93: 1k; RES-0402
SW3, SW4: SKQGADE010; SW4-SMD-5.2X5.2X1.5MM

Connections:
1KHZOUT50: IC5.B15 (IO_29)
3V3: C58.2, IC6.3 (DATA2), IC6.7 (DATA3), IC6.8 (VCC), JTAG0.4, R78.P$2, R79.P$2, R80.P$2, R82.P$2, R84.P$2, R91.P$2, R92.P$2
ASDO: IC5.D1 (IO_52), IC6.5 (DATA0)
BOARDIN0: IC5.C17 (IO_47)
BOARDIN1: IC5.D13 (IO_57)
BOARDIN2: IC5.D15 (IO_58)
BOARDIN3: IC5.D17 (IO_59)
BOARDIN5: IC5.E15 (IO_77)
BOARDIN6: IC5.E12 (IO_74)
BOARDIN7: IC5.E14 (IO_76)
BOARDOUT0: IC5.B17 (IO_31)
BOARDOUT1: IC5.B18 (IO_32)
BOARDOUT2: IC5.B19 (IO_33)
BOARDOUT3: IC5.B20 (IO_34)
BOARDOUT4: IC5.F13 (IO_88)
BOARDOUT5: IC5.F14 (IO_89)
BOARDOUT6: IC5.C13 (IO_45)
BOARDOUT7: IC5.C15 (IO_46)
CLKEXT: IC5.A12 (CLK8)
CLKOUT: IC5.E5 (IO_68)
CLKOUT2: IC5.E6 (IO_69)
CONF_DONE: IC5.M18 (CONF_DONE), R80.P$1
DA0_N: IC5.P3 (IO_181), R17.2
DA0_P: IC5.P4 (IO_182), R17.1
DA1_N: IC5.M6 (IO_158), R19.2
DA1_P: IC5.L6 (IO_148), R19.1
DA2_N: IC5.P7 (IO_185), R20.2
DA2_P: IC5.N7 (IO_170), R20.1
DA3_N: IC5.T7 (IO_209), R21.2
DA3_P: IC5.R7 (IO_196), R21.1
DA4_N: IC5.V5 (IO_242), R39.2
DA4_P: IC5.V6 (IO_243), R39.1
DA5_N: IC5.U8 (IO_224), R54.2
DA5_P: IC5.U7 (IO_223), R54.1
DA6_N: IC5.M1 (IO_153), R55.2
DA6_P: IC5.M2 (IO_154), R55.1
DA7_N: IC5.M3 (IO_155), R56.2
DA7_P: IC5.M4 (IO_156), R56.1
DA8_N: IC5.N1 (IO_166), R57.2
DA8_P: IC5.N2 (IO_167), R57.1
DA9_N: IC5.P1 (IO_179), R58.2
DA9_P: IC5.P2 (IO_180), R58.1
DA10_N: IC5.R1 (IO_192), R59.2
DA10_P: IC5.R2 (IO_193), R59.1
DA11_N: IC5.U1 (IO_221), R60.2
DA11_P: IC5.U2 (IO_222), R60.1
DACLK_N: IC5.T9 (IO_211), R61.2
DACLK_P: IC5.T8 (IO_210), R61.1
DASTR_N: IC5.T11 (IO_213), R62.2
DASTR_P: IC5.T10 (IO_212), R62.1
DATA0: IC5.K1 (IO_140), IC6.2 (DATA1)
DB0_N: IC5.H22 (IO_127), R63.2
DB0_P: IC5.H21 (IO_126), R63.1
DB1_N: IC5.J22 (IO_139), R64.2
DB1_P: IC5.J21 (IO_138), R64.1
DB2_N: IC5.K22 (IO_147), R65.2
DB2_P: IC5.K21 (IO_146), R65.1
DB3_N: IC5.L22 (IO_152), R66.2
DB3_P: IC5.L21 (IO_151), R66.1
DB4_N: IC5.M22 (IO_165), R67.2
DB4_P: IC5.M21 (IO_164), R67.1
DB5_N: IC5.K17 (IO_143), R68.2
DB5_P: IC5.K18 (IO_144), R68.1
DB6_N: IC5.M20 (IO_163), R69.2
DB6_P: IC5.M19 (IO_162), R69.1
DB7_N: IC5.N20 (IO_176), R70.2
DB7_P: IC5.N19 (IO_175), R70.1
DB8_N: IC5.N17 (IO_173), R71.2
DB8_P: IC5.N18 (IO_174), R71.1
DB9_N: IC5.R18 (IO_201), R72.2
DB9_P: IC5.R19 (IO_202), R72.1
DB10_N: IC5.U20 (IO_235), R73.2
DB10_P: IC5.U19 (IO_234), R73.1
DB11_N: IC5.Y17 (IO_279), R74.2
DB11_P: IC5.W17 (IO_265), R74.1
DBCLK_N: IC5.T15 (IO_217), R75.2
DBCLK_P: IC5.T14 (IO_216), R75.1
DBSTR_N: IC5.T13 (IO_215), R76.2
DBSTR_P: IC5.T12 (IO_214), R76.1
DC0_N: IC5.V1 (IO_238), R77.2
DC0_P: IC5.V2 (IO_239), R77.1
DC1_N: IC5.W1 (IO_256), R94.2
DC1_P: IC5.W2 (IO_257), R94.1
DC2_N: IC5.N8 (IO_171), R95.2
DC2_P: IC5.M8 (IO_160), R95.1
DC3_N: IC5.Y10 (IO_277), R96.2
DC3_P: IC5.W10 (IO_261), R96.1
DC4_N: IC5.U14 (IO_230), R97.2
DC4_P: IC5.V14 (IO_251), R97.1
DC5_N: IC5.V15 (IO_252), R98.2
DC5_P: IC5.U15 (IO_231), R98.1
DC6_N: IC5.U17 (IO_233), R99.2
DC6_P: IC5.U16 (IO_232), R99.1
DC7_N: IC5.Y1 (IO_270), R100.2
DC7_P: IC5.Y2 (IO_271), R100.1
DC8_N: IC5.AB5 (IO_301), R101.2
DC8_P: IC5.AA5 (IO_285), R101.1
DC9_N: IC5.Y7 (IO_275), R102.2
DC9_P: IC5.W7 (IO_259), R102.1
DC10_N: IC5.AB7 (IO_302), R103.2
DC10_P: IC5.AA7 (IO_286), R103.1
DC11_N: IC5.AB8 (IO_303), R104.2
DC11_P: IC5.AA8 (IO_287), R104.1
DCCLK_N: IC5.AB9 (IO_304), R105.2
DCCLK_P: IC5.AA9 (IO_288), R105.1
DCLK: IC5.K2 (DCLK), IC6.6 (DCLK)
DCSTR_N: IC5.AB10 (IO_305), R106.2
DCSTR_P: IC5.AA10 (IO_289), R106.1
DD0_N: IC5.N22 (IO_178), R107.2
DD0_P: IC5.N21 (IO_177), R107.1
DD1_N: IC5.P22 (IO_191), R108.2
DD1_P: IC5.P21 (IO_190), R108.1
DD2_N: IC5.R22 (IO_205), R109.2
DD2_P: IC5.R21 (IO_204), R109.1
DD3_N: IC5.U22 (IO_237), R110.2
DD3_P: IC5.U21 (IO_236), R110.1
DD4_N: IC5.V22 (IO_255), R111.2
DD4_P: IC5.V21 (IO_254), R111.1
DD5_N: IC5.Y22 (IO_281), R112.2
DD5_P: IC5.Y21 (IO_280), R112.1
DD6_N: IC5.W22 (IO_269), R113.2
DD6_P: IC5.W21 (IO_268), R113.1
DD7_N: IC5.AB20 (IO_313), R114.2
DD7_P: IC5.AA20 (IO_297), R114.1
DD8_N: IC5.AB17 (IO_310), R115.2
DD8_P: IC5.AA17 (IO_294), R115.1
DD9_N: IC5.AB16 (IO_309), R116.2
DD9_P: IC5.AA16 (IO_293), R116.1
DD10_N: IC5.AB15 (IO_308), R117.2
DD10_P: IC5.AA15 (IO_292), R117.1
DD11_N: IC5.AB14 (IO_307), R118.2
DD11_P: IC5.AA14 (IO_291), R118.1
DDCLK_N: IC5.AB13 (IO_306), R119.2
DDCLK_P: IC5.AA13 (IO_290), R119.1
DDSTR_N: IC5.Y13 (IO_278), R120.2
DDSTR_P: IC5.W13 (IO_262), R120.1
DEBUGOUT0: IC5.A13 (IO_9)
DEBUGOUT1: IC5.A14 (IO_10)
DEBUGOUT2: IC5.A15 (IO_11)
DEBUGOUT3: IC5.A16 (IO_12)
DEBUGOUT4: IC5.A17 (IO_13)
DEBUGOUT5: IC5.A18 (IO_14)
DEBUGOUT6: IC5.A19 (IO_15)
DEBUGOUT7: IC5.A20 (IO_16)
DEBUGOUT8: IC5.B13 (IO_27)
DEBUGOUT9: IC5.B14 (IO_28)
EXTTRIGIN: IC5.E16 (IO_78)
FAN_CONTROL: IC5.B16 (IO_30)
FTDI_AC0_RXF: IC5.B7 (IO_23)
FTDI_AC1_TXE: IC5.B4 (IO_20)
FTDI_AC2_RD: IC5.B8 (IO_24)
FTDI_AC3_WR: IC5.B3 (IO_19)
FTDI_AC5_CLK: IC5.A11 (CLK10)
FTDI_AC6_OE: IC5.A3 (IO_1)
FTDI_DATA0: IC5.G10 (IO_103)
FTDI_DATA1: IC5.A9 (IO_7)
FTDI_DATA2: IC5.D7 (IO_55)
FTDI_DATA3: IC5.C8 (IO_43)
FTDI_DATA4: IC5.C7 (IO_42)
FTDI_DATA5: IC5.C6 (IO_41)
FTDI_DATA6: IC5.C4 (IO_40)
FTDI_DATA7: IC5.C3 (IO_39)
GND: C58.1, C60.1, IC5.A1 (GND_1), IC5.A22 (GND_2), IC5.AA2 (GND_63), IC5.AA22 (GND_64), IC5.AB1 (GND_65), IC5.AB6 (GND_66), IC5.AB22 (GND_67), IC5.C5 (GND_3), IC5.C9 (GND_4), IC5.C11 (GND_5), IC5.C12 (GND_6), IC5.C14 (GND_7), IC5.C16 (GND_8), IC5.C18 (GND_9), IC5.D3 (GND_10), IC5.D8 (GND_11), IC5.E18 (GNDA2), IC5.E20 (GND_12), IC5.F3 (GND_13), IC5.F5 (GNDA3), IC5.F12 (GND_14), IC5.G2 (GND_15), IC5.G20 (GND_16), IC5.H3 (GND_17), IC5.H12 (GND_18), IC5.H13 (GND_19), IC5.J9 (GND_20), IC5.J15 (GND_21), IC5.J19 (GND_22), IC5.K3 (GND_23), IC5.K10 (GND_24), IC5.K11 (GND_25), IC5.K12 (GND_26), IC5.K13 (GND_27), IC5.K16 (GND_28), IC5.L10 (GND_29), IC5.L11 (GND_30), IC5.L12 (GND_31), IC5.L13 (GND_32), IC5.L15 (GND_33), IC5.L20 (GND_34), IC5.M10 (GND_35), IC5.M11 (GND_36), IC5.M12 (GND_37), IC5.M13 (GND_38), IC5.N3 (GND_39), IC5.N10 (GND_40), IC5.N11 (GND_41), IC5.N12 (GND_42), IC5.N13 (GND_43), IC5.N15 (GND_44), IC5.P8 (GND_45), IC5.P19 (GND_46), IC5.R3 (GND_47), IC5.R9 (GND_48), IC5.R11 (GND_49), IC5.R13 (GND_50), IC5.T20 (GND_51), IC5.U3 (GND_52), IC5.U5 (GNDA1), IC5.V18 (GNDA4), IC5.V20 (GND_53), IC5.W3 (GND_54), IC5.Y5 (GND_55), IC5.Y9 (GND_56), IC5.Y11 (GND_57), IC5.Y12 (GND_58), IC5.Y15 (GND_59), IC5.Y16 (GND_60), IC5.Y18 (GND_61), IC5.Y20 (GND_62), IC6.4 (GND), JTAG0.2, JTAG0.10, R81.P$2, R83.P$2, R85.P$2, R86.P$2, R93.P$1, SW3.4 (B1), SW4.4 (B1)
LED0: IC5.A5 (IO_3)
LED1: IC5.A6 (IO_4)
LED2: IC5.A7 (IO_5)
LED3: IC5.A8 (IO_6)
LVDSIN_CLK_N: IC5.G22 (CLK5), R23.2
LVDSIN_CLK_P: IC5.G21 (CLK4), R23.1
LVDSIN_SPARE0_N: IC5.E22 (IO_80), R25.2
LVDSIN_SPARE0_P: IC5.E21 (IO_79), R25.1
LVDSIN_TRIGB_N: IC5.H1 (IO_111), R26.2
LVDSIN_TRIGB_P: IC5.H2 (IO_112), R26.1
LVDSIN_TRIG_N: IC5.D22 (IO_63), R24.2
LVDSIN_TRIG_P: IC5.D21 (IO_62), R24.1
LVDSOUT_CLK_N: IC5.J1 (IO_128)
LVDSOUT_CLK_P: IC5.J2 (IO_129)
LVDSOUT_SPARE0_N: IC5.F1 (IO_81)
LVDSOUT_SPARE0_P: IC5.F2 (IO_82)
LVDSOUT_TRIGB_N: IC5.F22 (IO_96)
LVDSOUT_TRIGB_P: IC5.F21 (IO_95)
LVDSOUT_TRIG_N: IC5.G3 (IO_97)
LVDSOUT_TRIG_P: IC5.G4 (IO_98)
MSEL0: IC5.M17 (MSEL0), R83.P$1
MSEL1: IC5.L18 (MSEL1), R84.P$1
MSEL2: IC5.L17 (MSEL2), R85.P$1
MSEL3: IC5.K20 (MSEL3), R86.P$1
NCE: IC5.L3 (NCE), R81.P$1
NCONFIG: IC5.K5 (NCONFIG), R79.P$1, SW3.2 (A1)
NCSO: IC5.E2 (IO_65), IC6.1 (NCS)
NSTATUS: IC5.K6 (NSTATUS), R82.P$1
ORA0: IC5.C2 (IO_38)
ORA1: IC5.C1 (IO_37)
ORB0: IC5.B2 (IO_18)
ORB1: IC5.B1 (IO_17)
OSC_CLK_IN: IC5.B11 (CLK11)
RESET_IN: C60.2, IC5.D10 (IO_56), R78.P$1, SW4.2 (A1)
SCLK3: IC5.E10 (IO_72)
SCS3_ADC: IC5.F8 (IO_84)
SCS3_CLK: IC5.G11 (IO_104)
SCS3_IN1: IC5.G7 (IO_100)
SCS3_IN1DAC: IC5.G9 (IO_102)
SCS3_IN2: IC5.G8 (IO_101)
SCS3_SLOWADC: IC5.C10 (IO_44)
SDI3: IC5.F7 (IO_83)
SDO3_ADC: IC5.F10 (IO_86)
SDO3_IN1: IC5.A10 (IO_8)
SDO3_IN2: IC5.B9 (IO_25)
SDO3_SLOWADC: IC5.E9 (IO_71)
TCK: IC5.L2 (TCK), JTAG0.1, R93.P$2
TDI: IC5.L5 (TDI), JTAG0.9, R92.P$1
TDO: IC5.L4 (TDO), JTAG0.3
TMS: IC5.L1 (TMS), JTAG0.5, R91.P$1
VCCA: IC5.F18 (VCCA2), IC5.G6 (VCCA3), IC5.T6 (VCCA1), IC5.U18 (VCCA4)
VCCINT: IC5.G12 (VCCINT_1), IC5.H9 (VCCINT_2), IC5.J10 (VCCINT_3), IC5.J11 (VCCINT_4), IC5.J12 (VCCINT_5), IC5.J13 (VCCINT_6), IC5.J14 (VCCINT_7), IC5.J16 (VCCINT_8), IC5.K9 (VCCINT_9), IC5.K14 (VCCINT_10), IC5.K15 (VCCINT_11), IC5.L9 (VCCINT_12), IC5.L14 (VCCINT_13), IC5.L16 (VCCINT_14), IC5.M9 (VCCINT_15), IC5.M14 (VCCINT_16), IC5.M15 (VCCINT_17), IC5.N9 (VCCINT_18), IC5.N14 (VCCINT_19), IC5.P9 (VCCINT_20), IC5.P10 (VCCINT_21), IC5.P11 (VCCINT_22), IC5.P12 (VCCINT_23), IC5.P13 (VCCINT_24), IC5.P14 (VCCINT_25), IC5.R8 (VCCINT_26), IC5.R10 (VCCINT_27), IC5.R12 (VCCINT_28)
VCCIO2V5: IC5.A21 (VCCIO7_1), IC5.AA6 (VCCIO3_4), IC5.AB2 (VCCIO3_5), IC5.AB21 (VCCIO4_5), IC5.D4 (VCCIO1_1), IC5.D12 (VCCIO7_2), IC5.D14 (VCCIO7_3), IC5.D16 (VCCIO7_4), IC5.D18 (VCCIO7_5), IC5.E19 (VCCIO6_1), IC5.F4 (VCCIO1_2), IC5.G19 (VCCIO6_2), IC5.H4 (VCCIO1_3), IC5.J20 (VCCIO6_3), IC5.K4 (VCCIO1_4), IC5.L19 (VCCIO6_4), IC5.N4 (VCCIO2_1), IC5.P18 (VCCIO5_1), IC5.R4 (VCCIO2_2), IC5.T19 (VCCIO5_2), IC5.U4 (VCCIO2_3), IC5.V19 (VCCIO5_3), IC5.W4 (VCCIO2_4), IC5.W5 (VCCIO3_1), IC5.W9 (VCCIO3_2), IC5.W11 (VCCIO3_3), IC5.W12 (VCCIO4_1), IC5.W16 (VCCIO4_2), IC5.W18 (VCCIO4_3), IC5.Y14 (VCCIO4_4), IC5.Y19 (VCCIO5_4)
VCCIO3V3: IC5.A2 (VCCIO8_1), IC5.D5 (VCCIO8_2), IC5.D9 (VCCIO8_3), IC5.D11 (VCCIO8_4), IC5.E8 (VCCIO8_5)
VCCPLL: IC5.E17 (VCCD_PLL2), IC5.F6 (VCCD_PLL3), IC5.U6 (VCCD_PLL1), IC5.V17 (VCCD_PLL4)

Notes on the sheet:
All the inputs and outputs for the FPGA
GND for FPGA
Config and clocks for FPGA
Power for FPGA
JTAG interface for FPGA programming
Hard reset (reload firmware) and soft reset (send reset signal to firmware) buttons
Flash for FPGA programming
LVDS receivers require an external 100 Ohm termination resistor between the two signals at the input buffer We use 0201 resistors that fit on the bottom of the board and connect the vias under the FPGA for each LVDS input pair
For FPGA programming
