drandyhaas/HaasoscopePro/adc board/Kicad/Input_amps_1.kicad_sch

## KiCad design adc board/Kicad/Input_amps_1.kicad_sch (2025-04-30)

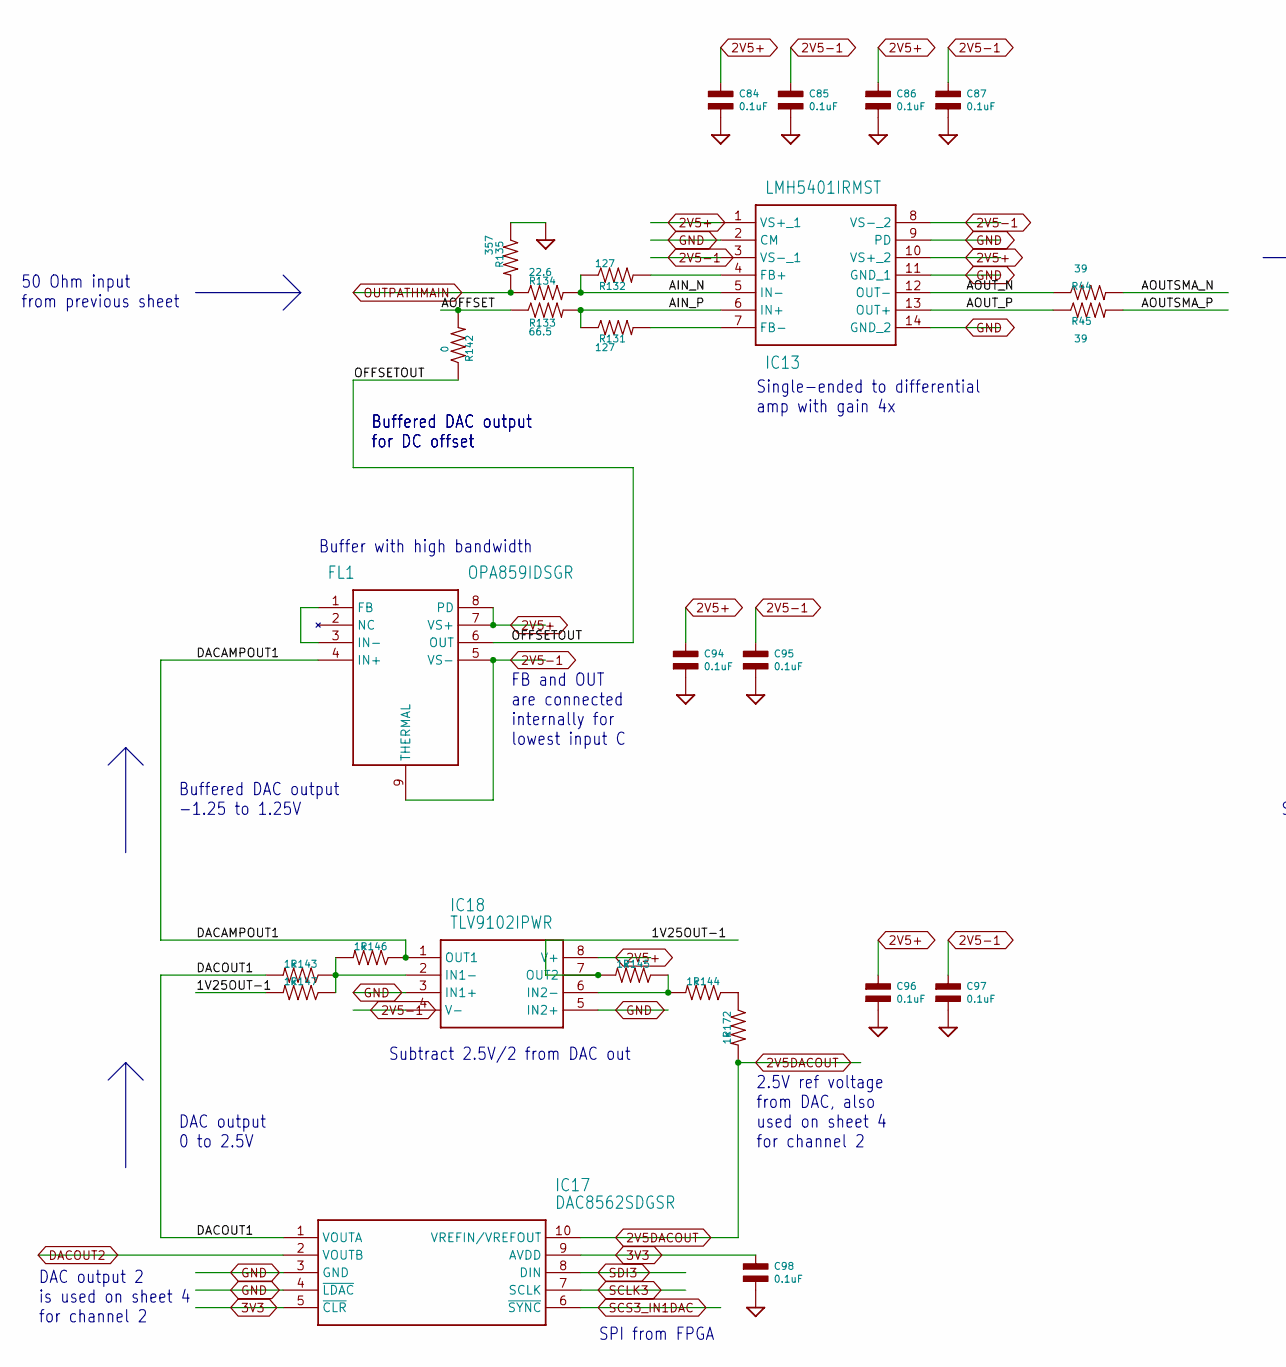
[picture p12: schematic Input_amps_1.kicad_sch, part in row 1, column 1]

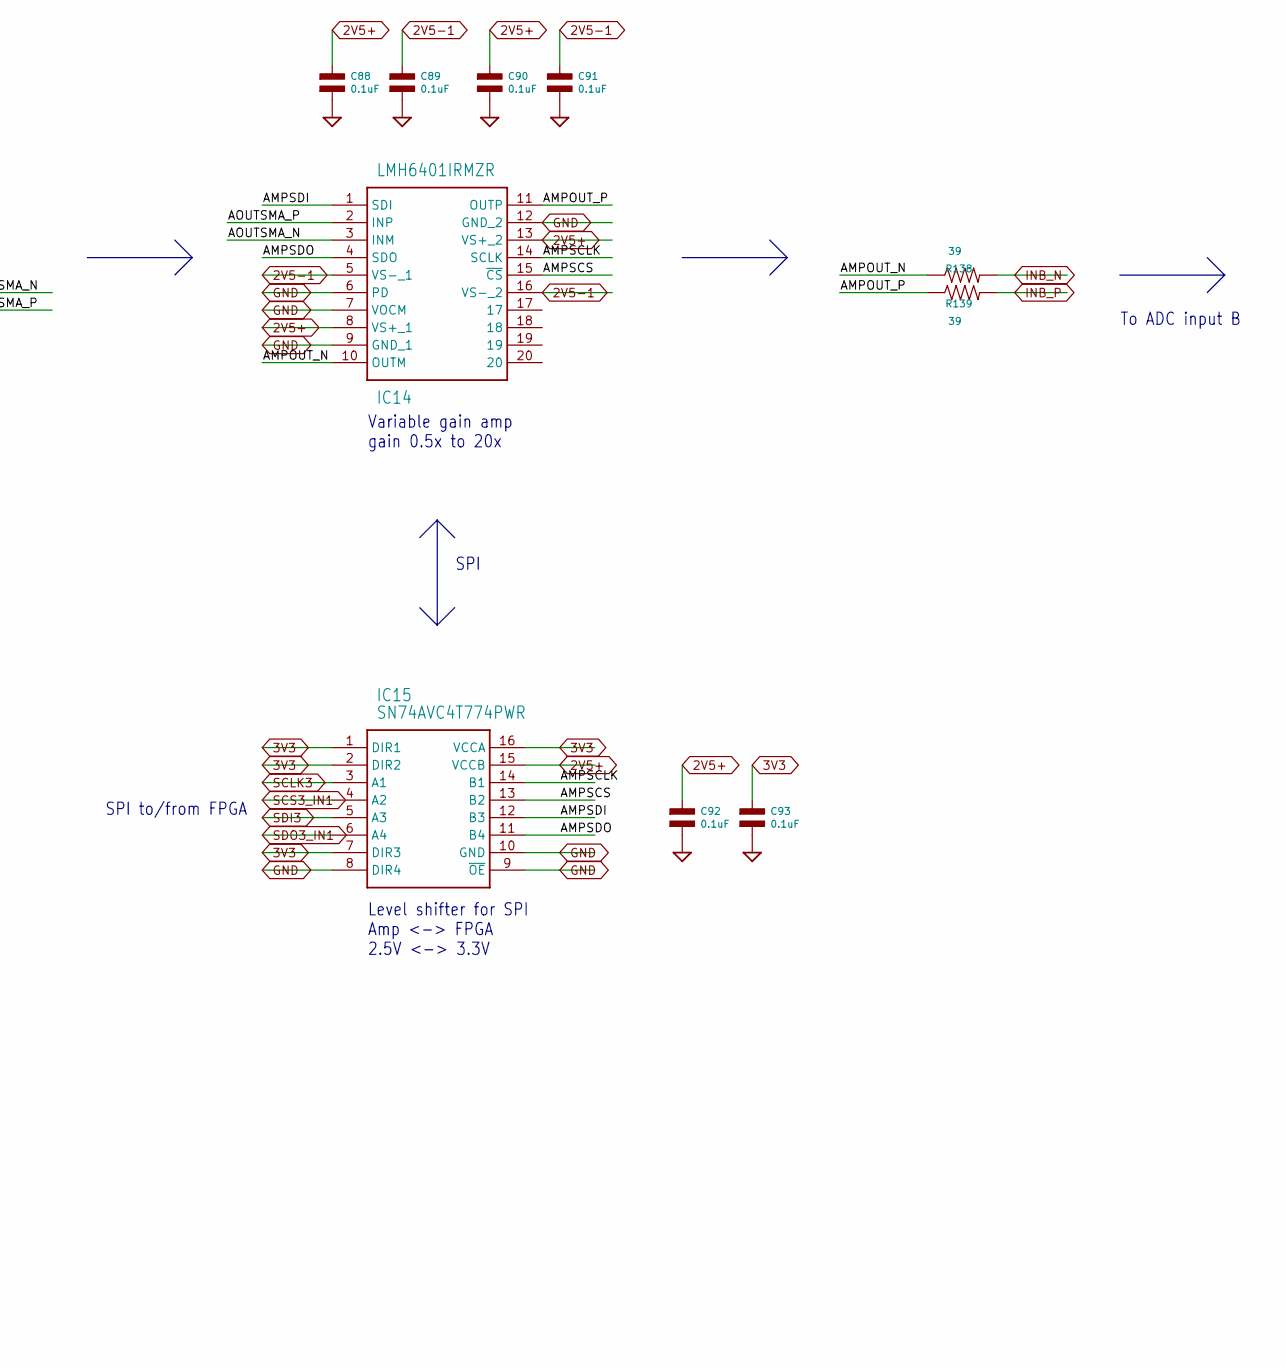
[picture p13: schematic Input_amps_1.kicad_sch, part in row 1, column 2]

Parts:
C84, C85, C86, C87, C88, C89, C90, C91, C92, C93, C94, C95, C96, C97, C98: 0.1uF; C0402
FL1: OPA859IDSGR; SON50P200X200X80-9N
IC13: LMH5401IRMST; LMH5401IRMSR
IC14: LMH6401IRMZR
IC15: SN74AVC4T774PWR; SOP65P640X120-16N
IC17: DAC8562SDGSR; SOP50P490X110-10N
IC18: TLV9102IPWR; SOP65P640X120-8N
R44, R45, R138, R139: 39; R0402
R131, R132: 127; R0402
R133: 66.5; R0402
R134: 22.6; R0402
R135: 357; R0402
R142: 0; R0402
R143, R144, R145, R146, R147, R172: 1k; R0402

Connections:
1V25OUT-1: IC18.7 (OUT2), R145.P$2, R147.P$2
2V5+: C84.P$1, C86.P$1, C88.P$1, C90.P$1, C92.P$1, C94.P$1, C96.P$1, FL1.7 (VS+), FL1.8 (PD), IC13.1 (VS+_1), IC13.10 (VS+_2), IC14.8 (VS+_1), IC14.13 (VS+_2), IC15.15 (VCCB), IC18.8 (V+)
2V5-1: C85.P$1, C87.P$1, C89.P$1, C91.P$1, C95.P$1, C97.P$1, FL1.5 (VS-), FL1.9 (THERMAL), IC13.3 (VS-_1), IC13.8 (VS-_2), IC14.5 (VS-_1), IC14.16 (VS-_2), IC18.4 (V-)
2V5DACOUT: IC17.10 (VREFIN/VREFOUT), R172.P$2
3V3: C93.P$1, C98.P$1, IC15.1 (DIR1), IC15.2 (DIR2), IC15.7 (DIR3), IC15.16 (VCCA), IC17.5 (~CLR), IC17.9 (AVDD)
AIN_N: IC13.5 (IN-), R132.P$1, R134.P$2
AIN_P: IC13.6 (IN+), R131.P$1, R133.P$2
AMPOUT_N: IC14.10 (OUTM), R138.P$1
AMPOUT_P: IC14.11 (OUTP), R139.P$1
AMPSCLK: IC14.14 (SCLK), IC15.14 (B1)
AMPSCS: IC14.15 (~CS), IC15.13 (B2)
AMPSDI: IC14.1 (SDI), IC15.12 (B3)
AMPSDO: IC14.4 (SDO), IC15.11 (B4)
AOFFSET: R133.P$1, R142.P$2
AOUTSMA_N: IC14.3 (INM), R44.P$2
AOUTSMA_P: IC14.2 (INP), R45.P$2
AOUT_N: IC13.12 (OUT-), R44.P$1
AOUT_P: IC13.13 (OUT+), R45.P$1
DACAMPOUT1: FL1.4 (IN+), IC18.1 (OUT1), R146.P$1
DACOUT1: IC17.1 (VOUTA), R143.P$2
DACOUT2: IC17.2 (VOUTB)
GND: C84.P$2, C85.P$2, C86.P$2, C87.P$2, C88.P$2, C89.P$2, C90.P$2, C91.P$2, C92.P$2, C93.P$2, C94.P$2, C95.P$2, C96.P$2, C97.P$2, C98.P$2, IC13.2 (CM), IC13.9 (PD), IC13.11 (GND_1), IC13.14 (GND_2), IC14.6 (PD), IC14.7 (VOCM), IC14.9 (GND_1), IC14.12 (GND_2), IC15.8 (DIR4), IC15.9 (~OE), IC15.10 (GND), IC17.3 (GND), IC17.4 (~LDAC), IC18.3 (IN1+), IC18.5 (IN2+), R135.P$1
INB_N: R138.P$2
INB_P: R139.P$2
unnamed: FL1.1 (FB), FL1.3 (IN-)
unnamed: IC13.4 (FB+), R132.P$2
unnamed: IC13.7 (FB-), R131.P$2
unnamed: IC18.2 (IN1-), R143.P$1, R146.P$2, R147.P$1
unnamed: IC18.6 (IN2-), R144.P$2, R145.P$1
unnamed: R144.P$1, R172.P$1
OFFSETOUT: FL1.6 (OUT), R142.P$1
OUTPATHMAIN: R134.P$1, R135.P$2
SCLK3: IC15.3 (A1), IC17.7 (SCLK)
SCS3_IN1: IC15.4 (A2)
SCS3_IN1DAC: IC17.6 (~SYNC)
SDI3: IC15.5 (A3), IC17.8 (DIN)
SDO3_IN1: IC15.6 (A4)

Notes on the sheet:
DAC output 2 is used on sheet 4 for channel 2
SPI from FPGA
Buffered DAC output for DC offset
DAC output 0 to 2.5V
To ADC input B
Level shifter for SPI Amp <-> FPGA 2.5V <-> 3.3V
SPI to/from FPGA
FB and OUT are connected internally for lowest input C
Single-ended to differential amp with gain 4x
Buffered DAC output -1.25 to 1.25V
Variable gain amp gain 0.5x to 20x
SPI
Subtract 2.5V/2 from DAC out
50 Ohm input from previous sheet
2.5V ref voltage from DAC, also used on sheet 4 for channel 2
Buffer with high bandwidth
