drandyhaas/HaasoscopePro/adc board/Kicad/Input_amps_2.kicad_sch

## KiCad design adc board/Kicad/Input_amps_2.kicad_sch (2025-04-30)

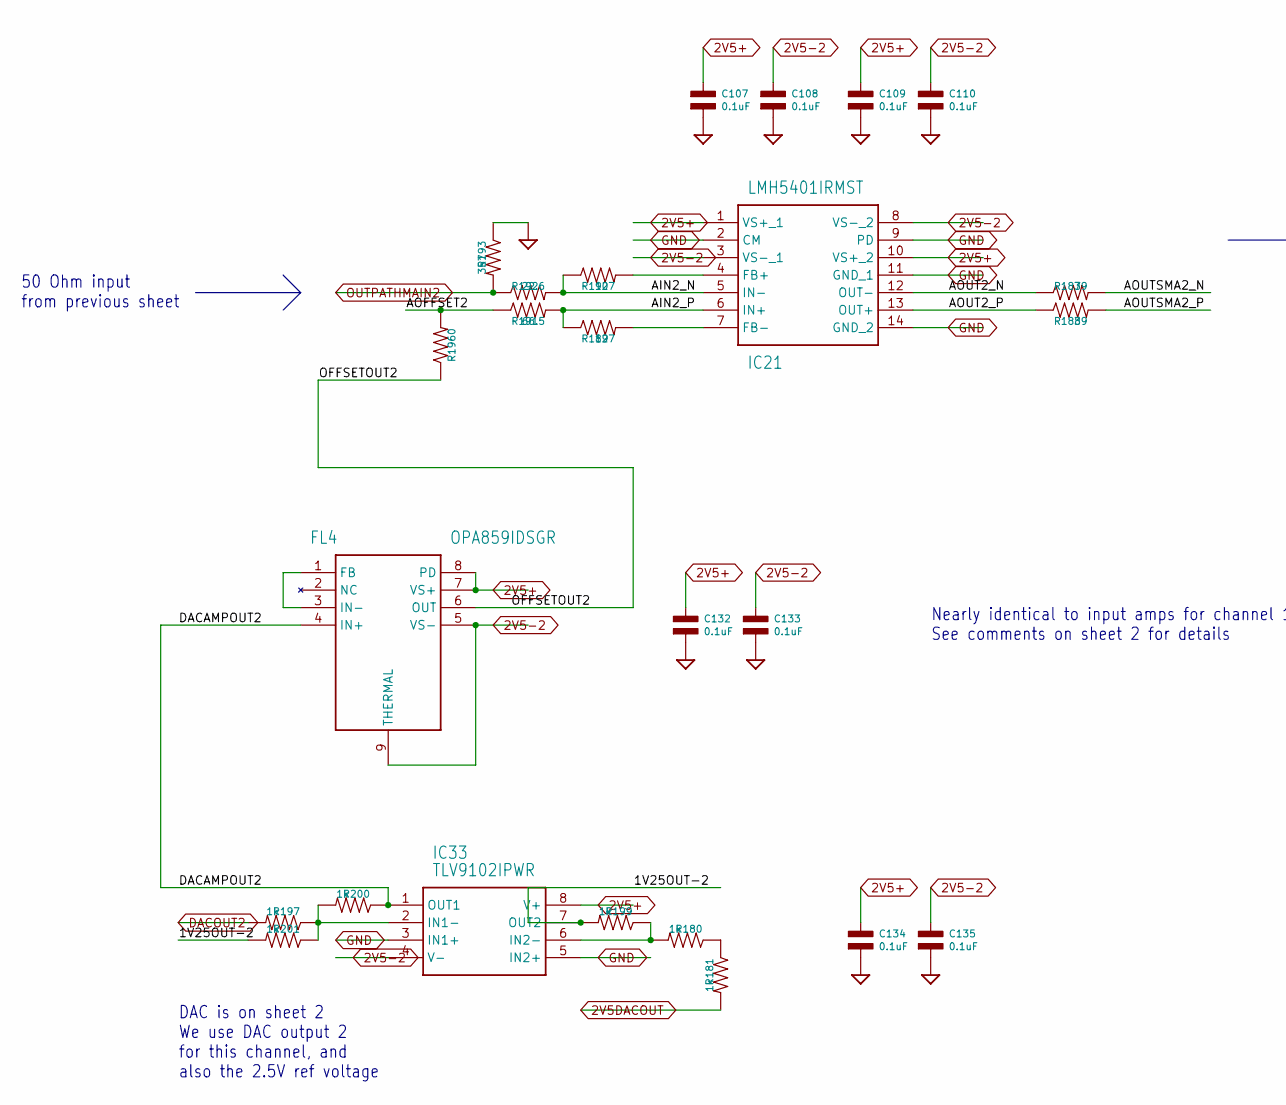
[picture p14: schematic Input_amps_2.kicad_sch, part in row 1, column 1]

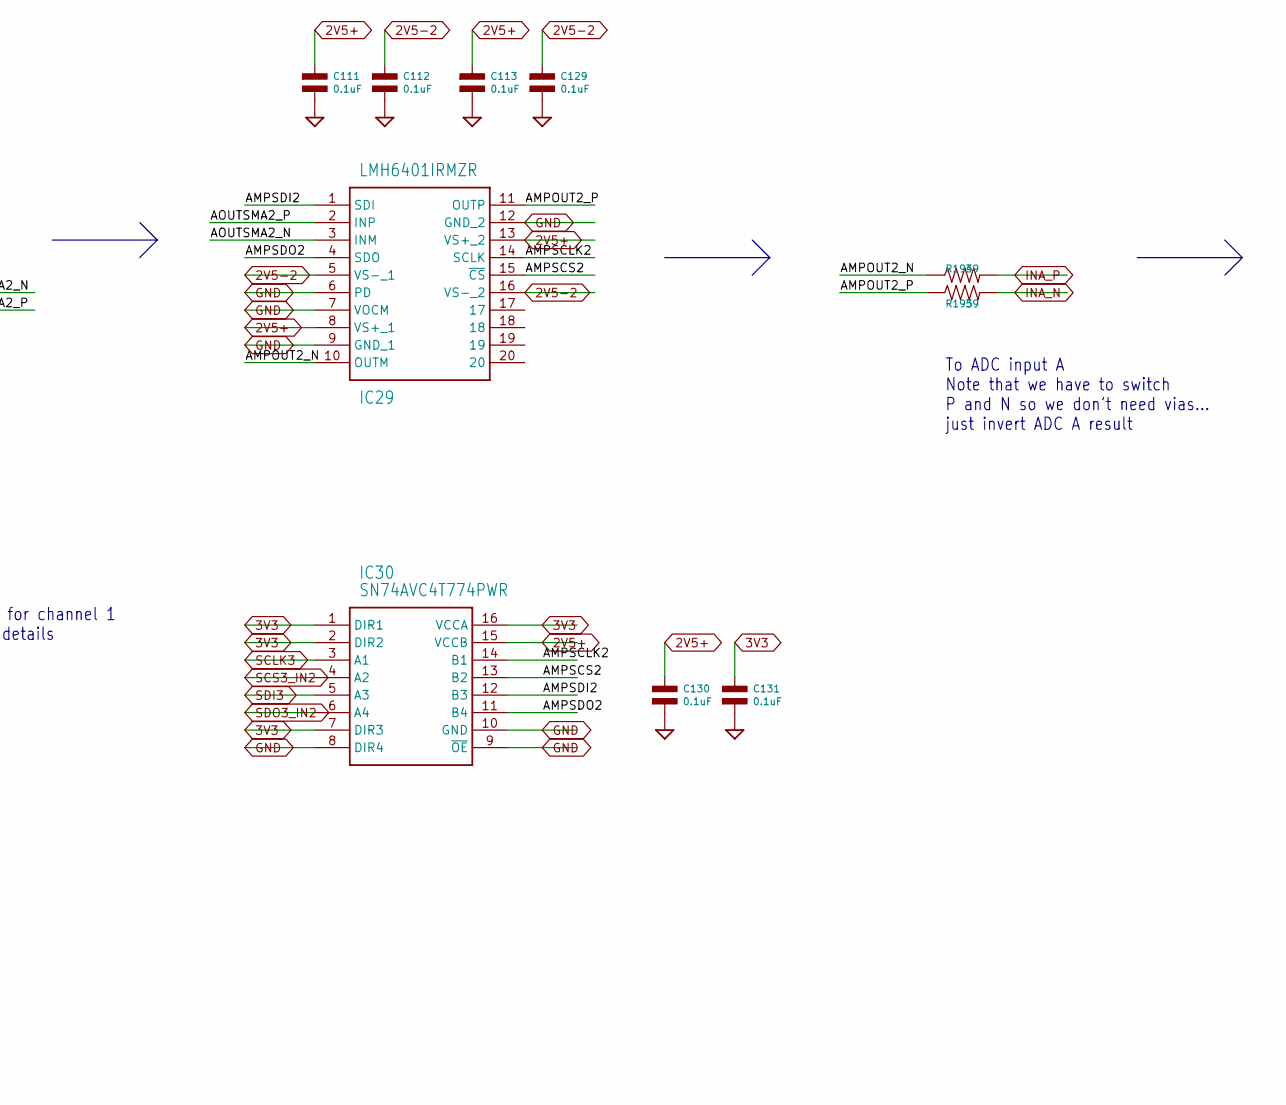
[picture p15: schematic Input_amps_2.kicad_sch, part in row 1, column 2]

Parts:
C107, C108, C109, C110, C111, C112, C113, C129, C130, C131, C132, C133, C134, C135: 0.1uF; C0402
FL4: OPA859IDSGR; SON50P200X200X80-9N
IC21: LMH5401IRMST; LMH5401IRMSR
IC29: LMH6401IRMZR
IC30: SN74AVC4T774PWR; SOP65P640X120-16N
IC33: TLV9102IPWR; SOP65P640X120-8N
R180, R181, R197, R199, R200, R201: 1k; R0402
R187, R188, R194, R195: 39; R0402
R189, R190: 127; R0402
R191: 66.5; R0402
R192: 22.6; R0402
R193: 357; R0402
R196: 0; R0402

Connections:
1V25OUT-2: IC33.7 (OUT2), R199.P$2, R201.P$2
2V5+: C107.P$1, C109.P$1, C111.P$1, C113.P$1, C130.P$1, C132.P$1, C134.P$1, FL4.7 (VS+), FL4.8 (PD), IC21.1 (VS+_1), IC21.10 (VS+_2), IC29.8 (VS+_1), IC29.13 (VS+_2), IC30.15 (VCCB), IC33.8 (V+)
2V5-2: C108.P$1, C110.P$1, C112.P$1, C129.P$1, C133.P$1, C135.P$1, FL4.5 (VS-), FL4.9 (THERMAL), IC21.3 (VS-_1), IC21.8 (VS-_2), IC29.5 (VS-_1), IC29.16 (VS-_2), IC33.4 (V-)
2V5DACOUT: R181.P$2
3V3: C131.P$1, IC30.1 (DIR1), IC30.2 (DIR2), IC30.7 (DIR3), IC30.16 (VCCA)
AIN2_N: IC21.5 (IN-), R190.P$1, R192.P$2
AIN2_P: IC21.6 (IN+), R189.P$1, R191.P$2
AMPOUT2_N: IC29.10 (OUTM), R194.P$1
AMPOUT2_P: IC29.11 (OUTP), R195.P$1
AMPSCLK2: IC29.14 (SCLK), IC30.14 (B1)
AMPSCS2: IC29.15 (~CS), IC30.13 (B2)
AMPSDI2: IC29.1 (SDI), IC30.12 (B3)
AMPSDO2: IC29.4 (SDO), IC30.11 (B4)
AOFFSET2: R191.P$1, R196.P$2
AOUT2_N: IC21.12 (OUT-), R187.P$1
AOUT2_P: IC21.13 (OUT+), R188.P$1
AOUTSMA2_N: IC29.3 (INM), R187.P$2
AOUTSMA2_P: IC29.2 (INP), R188.P$2
DACAMPOUT2: FL4.4 (IN+), IC33.1 (OUT1), R200.P$1
DACOUT2: R197.P$2
GND: C107.P$2, C108.P$2, C109.P$2, C110.P$2, C111.P$2, C112.P$2, C113.P$2, C129.P$2, C130.P$2, C131.P$2, C132.P$2, C133.P$2, C134.P$2, C135.P$2, IC21.2 (CM), IC21.9 (PD), IC21.11 (GND_1), IC21.14 (GND_2), IC29.6 (PD), IC29.7 (VOCM), IC29.9 (GND_1), IC29.12 (GND_2), IC30.8 (DIR4), IC30.9 (~OE), IC30.10 (GND), IC33.3 (IN1+), IC33.5 (IN2+), R193.P$1
INA_N: R195.P$2
INA_P: R194.P$2
unnamed: FL4.1 (FB), FL4.3 (IN-)
unnamed: IC21.4 (FB+), R190.P$2
unnamed: IC21.7 (FB-), R189.P$2
unnamed: IC33.2 (IN1-), R197.P$1, R200.P$2, R201.P$1
unnamed: IC33.6 (IN2-), R180.P$2, R199.P$1
unnamed: R180.P$1, R181.P$1
OFFSETOUT2: FL4.6 (OUT), R196.P$1
OUTPATHMAIN2: R192.P$1, R193.P$2
SCLK3: IC30.3 (A1)
SCS3_IN2: IC30.4 (A2)
SDI3: IC30.5 (A3)
SDO3_IN2: IC30.6 (A4)

Notes on the sheet:
To ADC input A Note that we have to switch P and N so we don't need vias... just invert ADC A result
DAC is on sheet 2 We use DAC output 2 for this channel, and also the 2.5V ref voltage
50 Ohm input from previous sheet
Nearly identical to input amps for channel 1 See comments on sheet 2 for details
