drandyhaas/HaasoscopePro/adc board/Kicad/Other_FPGA_IO.kicad_sch

## KiCad design adc board/Kicad/Other_FPGA_IO.kicad_sch (2025-04-30)

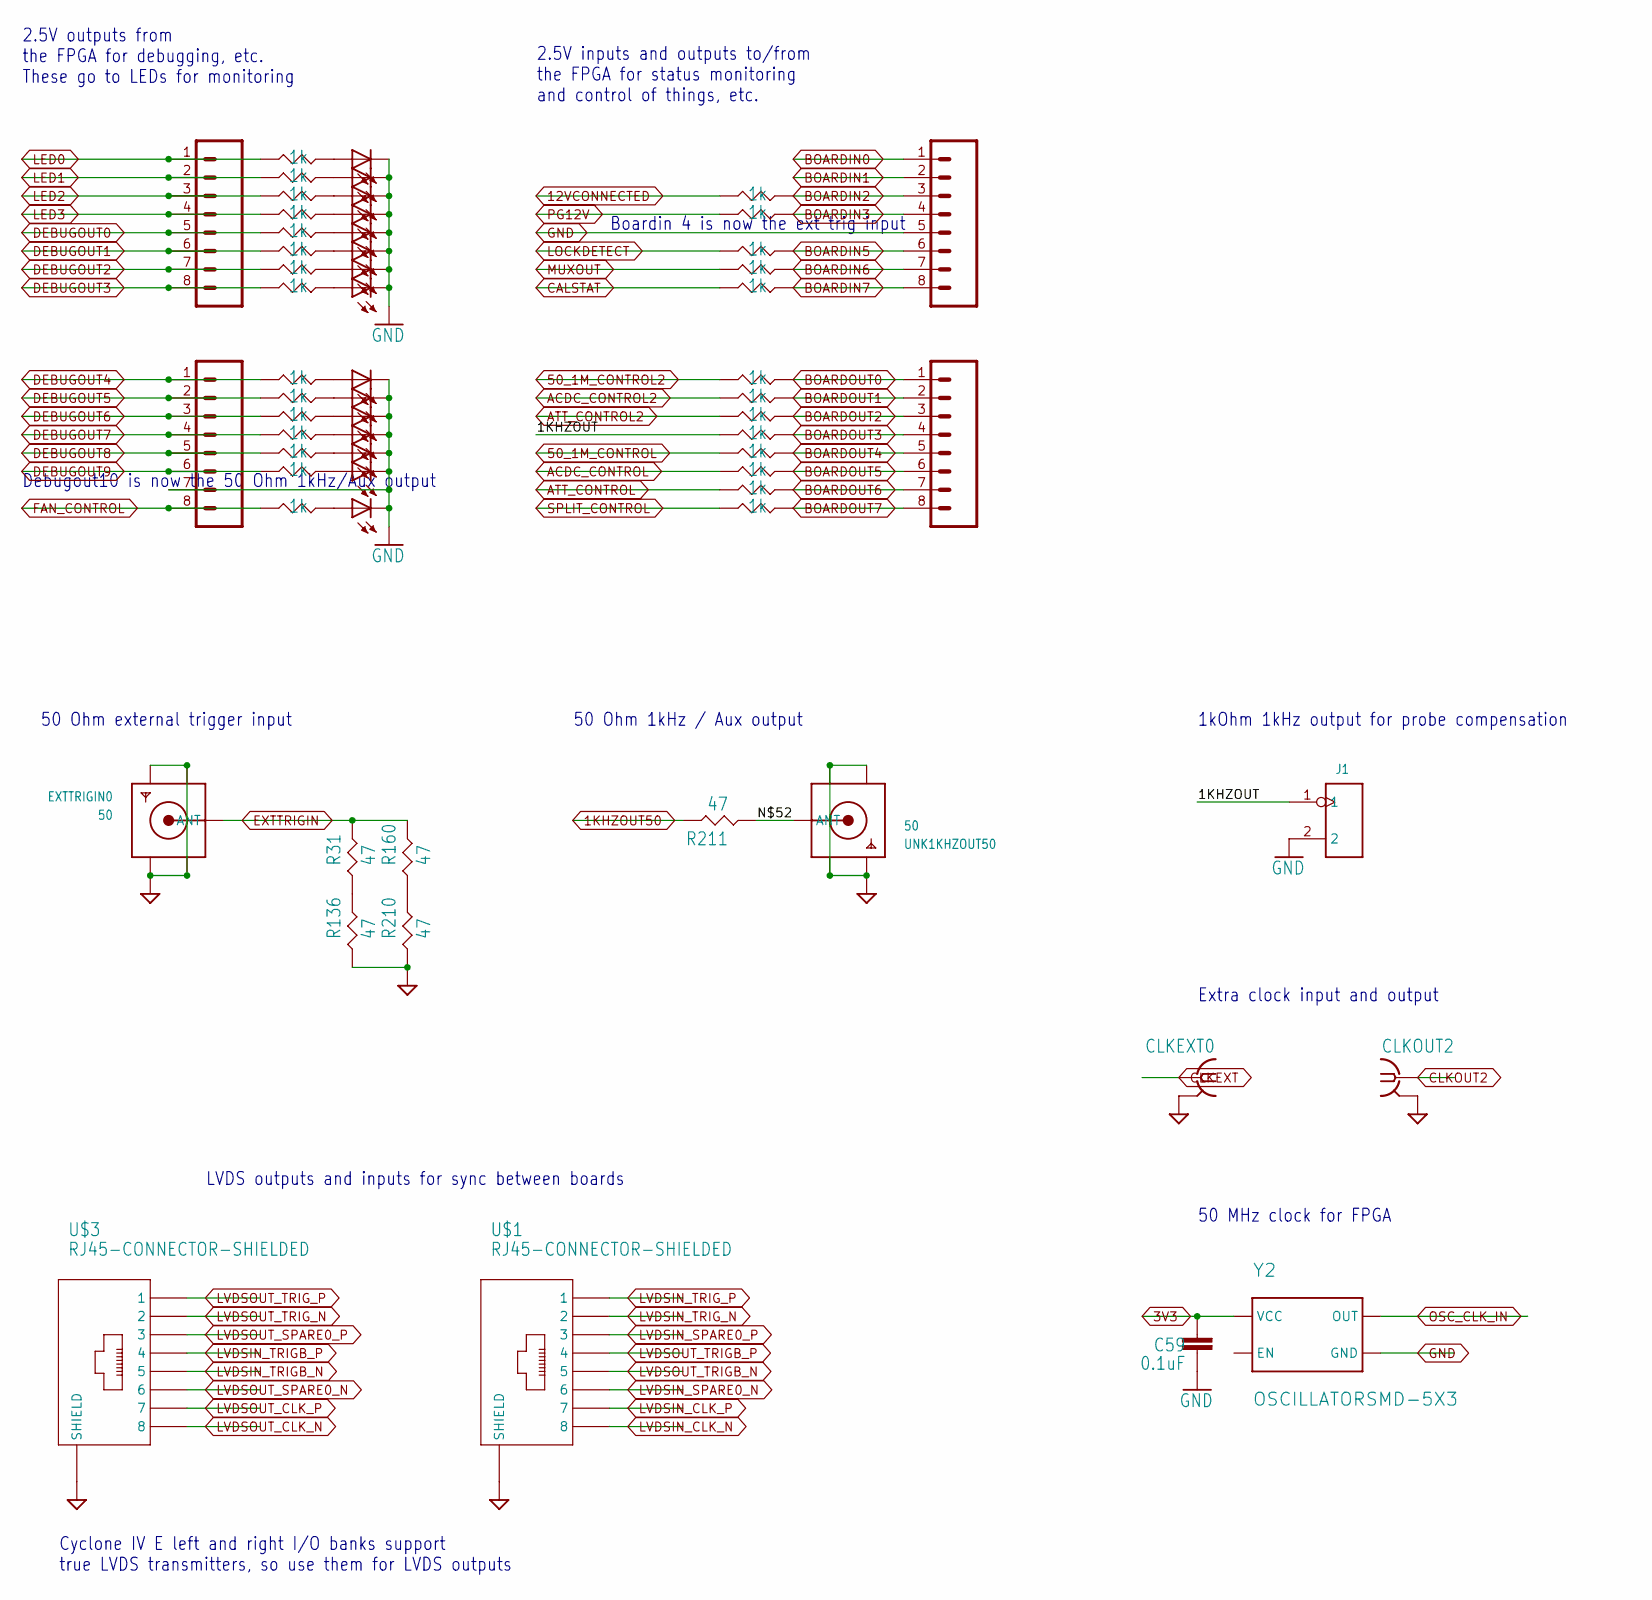
[picture p16: schematic Other_FPGA_IO.kicad_sch]

Parts:
C59: 0.1uF; RESC0402_N
CLKEXT0: BU-SMB-V
CLKOUT2: BU-SMB-V
EXTTRIGIN0: 50; SMA_EDGELAUNCH
J1: 2p-2.54; H2-2.54
J8, J10, J11, J13: 8pin; 1X08
LED25, LED26, LED27, LED28, LED29, LED30, LED32, LED41, LED42, LED43, LED44, LED45, LED46, LED47, LED48: red; CHIP-LED0603
R6, R7, R8, R9, R10, R11, R12, R13, R16, R22, R30, R32, R33, R34, R35, R36, R37, R46, R47, R48, R49, R50, R51, R52, R53, R206, R236, R238: 1k; RES-0402
R31, R136, R160, R210, R211: 47; RES-0402
U$1, U$3: RJ45-CONNECTOR-SHIELDED; RJ45_THT_RA_AMPH-FRJAE448
UNK1KHZOUT50: 50; SMA_EDGELAUNCH
Y2: OSCILLATORSMD-5X3; OSCILLATOR-SMD-5X3.2; LCSC C2901546

Connections:
1KHZOUT: J1.1, R206.P$1
1KHZOUT50: R211.P$2
3V3: C59.2, Y2.4 (VCC)
12VCONNECTED: R238.P$1
50_1M_CONTROL: R8.P$1
50_1M_CONTROL2: R12.P$1
ACDC_CONTROL: R9.P$1
ACDC_CONTROL2: R13.P$1
ATT_CONTROL: R10.P$1
ATT_CONTROL2: R22.P$1
BOARDIN0: J8.1
BOARDIN1: J8.2
BOARDIN2: J8.3, R238.P$2
BOARDIN3: J8.4, R236.P$2
BOARDIN5: J8.6, R7.P$2
BOARDIN6: J8.7, R6.P$2
BOARDIN7: J8.8, R16.P$2
BOARDOUT0: J10.1, R12.P$2
BOARDOUT1: J10.2, R13.P$2
BOARDOUT2: J10.3, R22.P$2
BOARDOUT3: J10.4, R206.P$2
BOARDOUT4: J10.5, R8.P$2
BOARDOUT5: J10.6, R9.P$2
BOARDOUT6: J10.7, R10.P$2
BOARDOUT7: J10.8, R11.P$2
CALSTAT: R16.P$1
CLKEXT: CLKEXT0.1
CLKOUT2: CLKOUT2.1
DEBUGOUT0: J13.5, R49.P$1
DEBUGOUT1: J13.6, R48.P$1
DEBUGOUT2: J13.7, R47.P$1
DEBUGOUT3: J13.8, R46.P$1
DEBUGOUT4: J11.1, R37.P$1
DEBUGOUT5: J11.2, R36.P$1
DEBUGOUT6: J11.3, R35.P$1
DEBUGOUT7: J11.4, R34.P$1
DEBUGOUT8: J11.5, R33.P$1
DEBUGOUT9: J11.6, R32.P$1
EXTTRIGIN: EXTTRIGIN0.P (ANT), R31.P$2, R160.P$2
FAN_CONTROL: J11.8, R30.P$1
GND: C59.1, CLKEXT0.2, CLKEXT0.3 (2), CLKEXT0.4 (2), CLKEXT0.5 (2), CLKOUT2.2, CLKOUT2.3 (2), CLKOUT2.4 (2), CLKOUT2.5 (2), EXTTRIGIN0.GND@1 (GND4), EXTTRIGIN0.GND@2 (GND3), EXTTRIGIN0.GND@3 (GND2), EXTTRIGIN0.GND@4 (GND1), J1.2, J8.5, J11.7, LED25.C, LED26.C, LED27.C, LED28.C, LED29.C, LED30.C, LED32.C, LED41.C, LED42.C, LED43.C, LED44.C, LED45.C, LED46.C, LED47.C, LED48.C, R136.P$1, R210.P$1, U$1.S$1 (SHIELD), U$1.S$2 (SHIELD), U$1.S$3 (SHIELD), U$1.S$4 (SHIELD), U$3.S$1 (SHIELD), U$3.S$2 (SHIELD), U$3.S$3 (SHIELD), U$3.S$4 (SHIELD), UNK1KHZOUT50.GND@1 (GND4), UNK1KHZOUT50.GND@2 (GND3), UNK1KHZOUT50.GND@3 (GND2), UNK1KHZOUT50.GND@4 (GND1), Y2.2 (GND)
LED0: J13.1, R53.P$1
LED1: J13.2, R52.P$1
LED2: J13.3, R51.P$1
LED3: J13.4, R50.P$1
LOCKDETECT: R7.P$1
LVDSIN_CLK_N: U$1.P$8 (8)
LVDSIN_CLK_P: U$1.P$7 (7)
LVDSIN_SPARE0_N: U$1.P$6 (6)
LVDSIN_SPARE0_P: U$1.P$3 (3)
LVDSIN_TRIGB_N: U$3.P$5 (5)
LVDSIN_TRIGB_P: U$3.P$4 (4)
LVDSIN_TRIG_N: U$1.P$2 (2)
LVDSIN_TRIG_P: U$1.P$1 (1)
LVDSOUT_CLK_N: U$3.P$8 (8)
LVDSOUT_CLK_P: U$3.P$7 (7)
LVDSOUT_SPARE0_N: U$3.P$6 (6)
LVDSOUT_SPARE0_P: U$3.P$3 (3)
LVDSOUT_TRIGB_N: U$1.P$5 (5)
LVDSOUT_TRIGB_P: U$1.P$4 (4)
LVDSOUT_TRIG_N: U$3.P$2 (2)
LVDSOUT_TRIG_P: U$3.P$1 (1)
MUXOUT: R6.P$1
unnamed: R211.P$1, UNK1KHZOUT50.P (ANT)
unnamed: LED25.A, R37.P$2
unnamed: LED26.A, R36.P$2
unnamed: LED27.A, R35.P$2
unnamed: LED28.A, R34.P$2
unnamed: LED29.A, R33.P$2
unnamed: LED30.A, R32.P$2
unnamed: LED32.A, R30.P$2
unnamed: LED41.A, R53.P$2
unnamed: LED42.A, R52.P$2
unnamed: LED43.A, R51.P$2
unnamed: LED44.A, R50.P$2
unnamed: LED45.A, R49.P$2
unnamed: LED46.A, R48.P$2
unnamed: LED47.A, R47.P$2
unnamed: LED48.A, R46.P$2
unnamed: R31.P$1, R136.P$2
unnamed: R160.P$1, R210.P$2
OSC_CLK_IN: Y2.3 (OUT)
PG12V: R236.P$1
SPLIT_CONTROL: R11.P$1

Notes on the sheet:
50 Ohm 1kHz / Aux output
2.5V inputs and outputs to/from the FPGA for status monitoring and control of things, etc.
2.5V outputs from the FPGA for debugging, etc. These go to LEDs for monitoring
50 Ohm external trigger input
Extra clock input and output
LVDS outputs and inputs for sync between boards
Debugout10 is now the 50 Ohm 1kHz/Aux output
Cyclone IV E left and right I/O banks support true LVDS transmitters, so use them for LVDS outputs
1kOhm 1kHz output for probe compensation
50 MHz clock for FPGA
Boardin 4 is now the ext trig input
