drandyhaas/HaasoscopePro/adc board/Kicad/Power_-_12V.kicad_sch

## KiCad design adc board/Kicad/Power_-_12V.kicad_sch (2025-04-30)

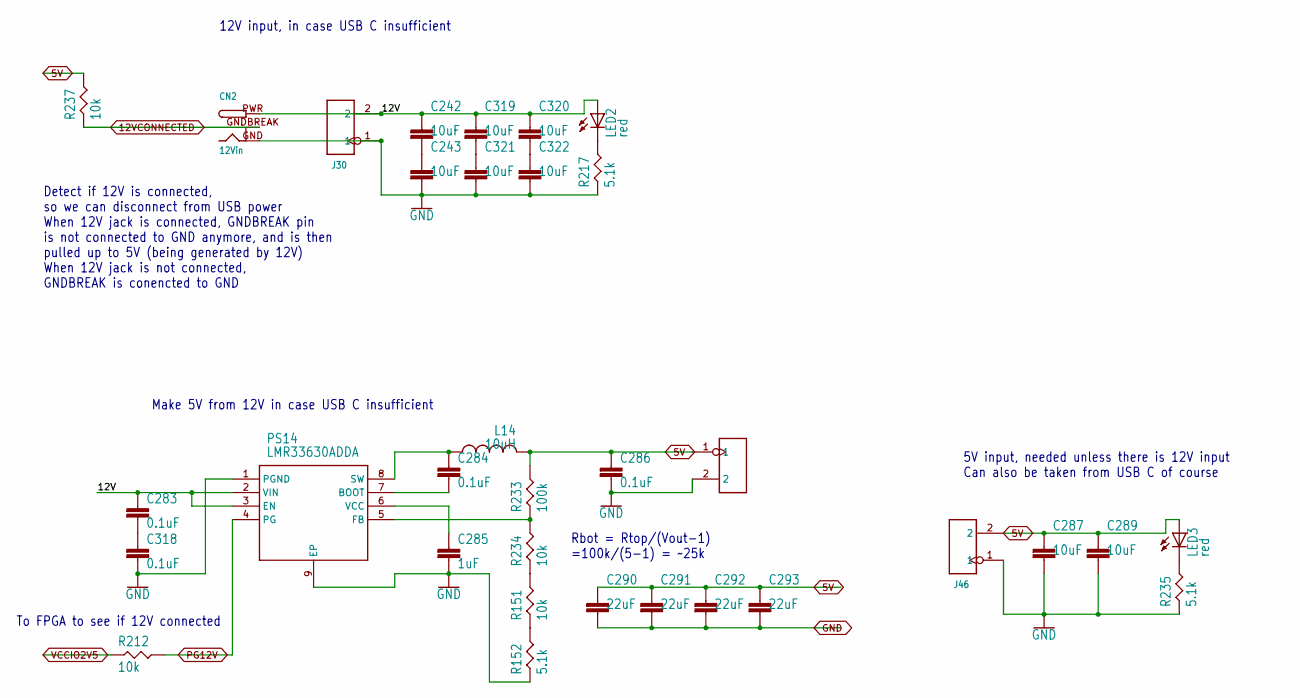
[picture p17: schematic Power_-_12V.kicad_sch]

Parts:
C242, C243, C287, C289, C319, C320, C321, C322: 10uF; RESC0805_N
C283, C318: 0.1uF; RESC0402_N; LCSC C307331
C284, C286: 0.1uF; RESC0402_N
C285: 1uF; RESC0402_N
C290, C291, C292, C293: 22uF; RESC0805_N
CN2: 12Vin; DCJACK_2MM_PTH
J30, J45, J46: 2p-2.54; H2-2.54
L14: 10uH; CDRH125; LCSC C339970
LED2, LED3: red; CHIP-LED0603
PS14: LMR33630ADDA; SOIC127P600X170-9N; LCSC C841384
R151, R212, R234, R237: 10k; RES-0402
R152, R217, R235: 5.1k; RES-0402
R233: 100k; RES-0402

Connections:
5V: C286.1, C287.1, C289.1, C290.1, C291.1, C292.1, C293.1, J45.1, J46.2, L14.2, LED3.A, R233.P$2, R237.P$2
12V: C242.1, C283.1, C319.1, C320.1, CN2.PWR, J30.2, LED2.A, PS14.2 (VIN), PS14.3 (EN)
12VCONNECTED: CN2.GNDBREAK, R237.P$1
GND: C243.2, C285.2, C286.2, C287.2, C289.2, C290.2, C291.2, C292.2, C293.2, C318.2, C321.2, C322.2, CN2.GND, J30.1, J45.2, J46.1, PS14.1 (PGND), PS14.9 (EP), R152.P$1, R217.P$1, R235.P$1
unnamed: C242.2, C243.1
unnamed: C283.2, C318.1
unnamed: C284.1, L14.1, PS14.8 (SW)
unnamed: C284.2, PS14.7 (BOOT)
unnamed: C285.1, PS14.6 (VCC)
unnamed: C319.2, C321.1
unnamed: C320.2, C322.1
unnamed: LED2.C, R217.P$2
unnamed: LED3.C, R235.P$2
unnamed: PS14.5 (FB), R233.P$1, R234.P$2
unnamed: R151.P$1, R152.P$2
unnamed: R151.P$2, R234.P$1
PG12V: PS14.4 (PG), R212.P$2
VCCIO2V5: R212.P$1

Notes on the sheet:
Make 5V from 12V in case USB C insufficient
12V input, in case USB C insufficient
Detect if 12V is connected, so we can disconnect from USB power When 12V jack is connected, GNDBREAK pin is not connected to GND anymore, and is then pulled up to 5V (being generated by 12V) When 12V jack is not connected, GNDBREAK is conencted to GND
5V input, needed unless there is 12V input Can also be taken from USB C of course
To FPGA to see if 12V connected
Rbot = Rtop/(Vout-1) =100k/(5-1) = ~25k
