drandyhaas/HaasoscopePro/adc board/Kicad/Power_-_ADC.kicad_sch

## KiCad design adc board/Kicad/Power_-_ADC.kicad_sch (2025-04-30)

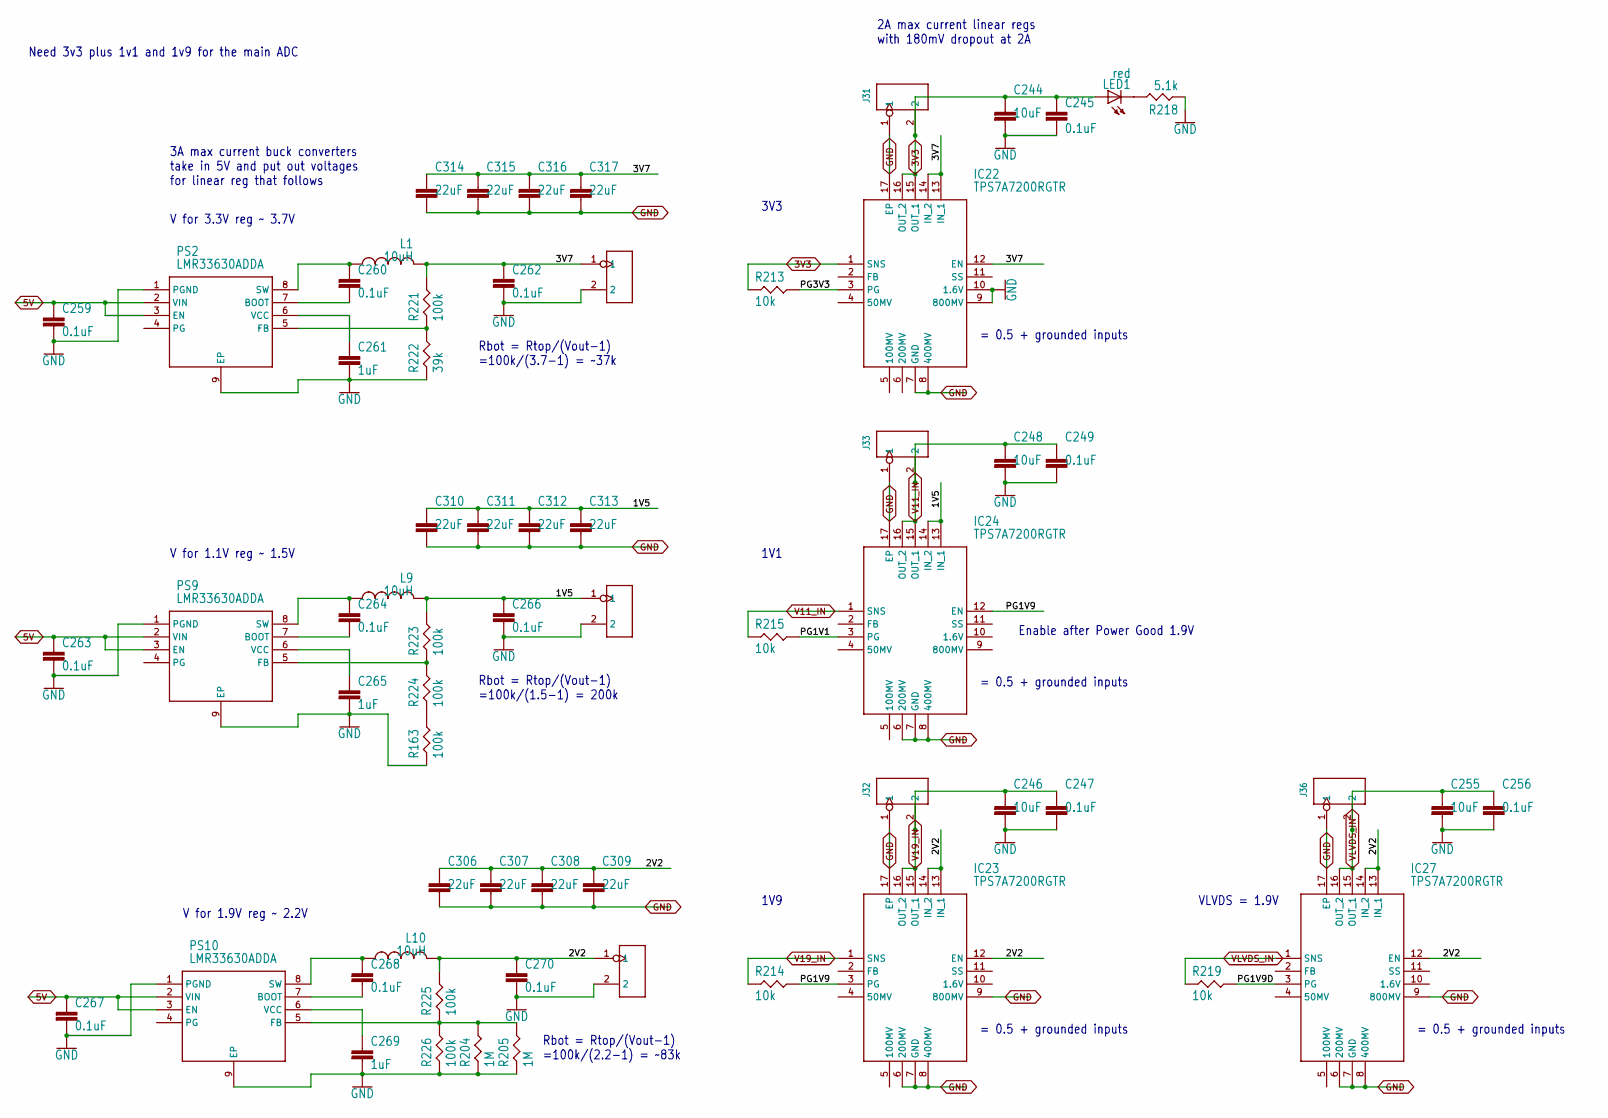
[picture p18: schematic Power_-_ADC.kicad_sch]

Parts:
C244, C246, C248, C255: 10uF; RESC0805_N
C245, C247, C249, C256, C259, C260, C262, C263, C264, C266, C267, C268, C270: 0.1uF; RESC0402_N
C261, C265, C269: 1uF; RESC0402_N
C306, C307, C308, C309, C310, C311, C312, C313, C314, C315, C316, C317: 22uF; RESC0805_N
IC22, IC23, IC24, IC27: TPS7A7200RGTR; QFN50P300X300X100-17N
J31, J32, J33, J36, J39, J40, J41: 2p-2.54; H2-2.54
L1, L9, L10: 10uH; CDRH125; LCSC C339970
LED1: red; CHIP-LED0603
PS2, PS9, PS10: LMR33630ADDA; SOIC127P600X170-9N; LCSC C841384
R163, R221, R223, R224, R225, R226: 100k; RES-0402
R204, R205: 1M; RES-0402
R213, R214, R215, R219: 10k; RES-0402
R218: 5.1k; RES-0402
R222: 39k; RES-0402

Connections:
1V5: C266.1, C310.1, C311.1, C312.1, C313.1, IC24.13 (IN_1), IC24.14 (IN_2), J40.1, L9.2, R223.P$2
2V2: C270.1, C306.1, C307.1, C308.1, C309.1, IC23.12 (EN), IC23.13 (IN_1), IC23.14 (IN_2), IC27.12 (EN), IC27.13 (IN_1), IC27.14 (IN_2), J41.1, L10.2, R225.P$2
3V3: C244.1, C245.1, IC22.1 (SNS), IC22.15 (OUT_1), IC22.16 (OUT_2), J31.2, LED1.A, R213.P$1
3V7: C262.1, C314.1, C315.1, C316.1, C317.1, IC22.12 (EN), IC22.13 (IN_1), IC22.14 (IN_2), J39.1, L1.2, R221.P$2
5V: C259.1, C263.1, C267.1, PS2.2 (VIN), PS2.3 (EN), PS9.2 (VIN), PS9.3 (EN), PS10.2 (VIN), PS10.3 (EN)
GND: C244.2, C245.2, C246.2, C247.2, C248.2, C249.2, C255.2, C256.2, C259.2, C261.2, C262.2, C263.2, C265.2, C266.2, C267.2, C269.2, C270.2, C306.2, C307.2, C308.2, C309.2, C310.2, C311.2, C312.2, C313.2, C314.2, C315.2, C316.2, C317.2, IC22.7 (GND), IC22.8 (400MV), IC22.9 (800MV), IC22.10 (1.6V), IC22.17 (EP), IC23.6 (200MV), IC23.7 (GND), IC23.8 (400MV), IC23.9 (800MV), IC23.17 (EP), IC24.6 (200MV), IC24.7 (GND), IC24.8 (400MV), IC24.17 (EP), IC27.6 (200MV), IC27.7 (GND), IC27.8 (400MV), IC27.9 (800MV), IC27.17 (EP), J31.1, J32.1, J33.1, J36.1, J39.2, J40.2, J41.2, PS2.1 (PGND), PS2.9 (EP), PS9.1 (PGND), PS9.9 (EP), PS10.1 (PGND), PS10.9 (EP), R163.P$1, R204.P$1, R205.P$1, R218.P$1, R222.P$1, R226.P$1
unnamed: C260.1, L1.1, PS2.8 (SW)
unnamed: C260.2, PS2.7 (BOOT)
unnamed: C261.1, PS2.6 (VCC)
unnamed: C264.1, L9.1, PS9.8 (SW)
unnamed: C264.2, PS9.7 (BOOT)
unnamed: C265.1, PS9.6 (VCC)
unnamed: C268.1, L10.1, PS10.8 (SW)
unnamed: C268.2, PS10.7 (BOOT)
unnamed: C269.1, PS10.6 (VCC)
unnamed: LED1.C, R218.P$2
unnamed: PS2.5 (FB), R221.P$1, R222.P$2
unnamed: PS9.5 (FB), R223.P$1, R224.P$2
unnamed: PS10.5 (FB), R204.P$2, R205.P$2, R225.P$1, R226.P$2
unnamed: R163.P$2, R224.P$1
PG1V1: IC24.3 (PG), R215.P$2
PG1V9: IC23.3 (PG), IC24.12 (EN), R214.P$2
PG1V9D: IC27.3 (PG), R219.P$2
PG3V3: IC22.3 (PG), R213.P$2
V11_IN: C248.1, C249.1, IC24.1 (SNS), IC24.15 (OUT_1), IC24.16 (OUT_2), J33.2, R215.P$1
V19_IN: C246.1, C247.1, IC23.1 (SNS), IC23.15 (OUT_1), IC23.16 (OUT_2), J32.2, R214.P$1
VLVDS_IN: C255.1, C256.1, IC27.1 (SNS), IC27.15 (OUT_1), IC27.16 (OUT_2), J36.2, R219.P$1

Notes on the sheet:
1V9
1V1
3V3
V for 1.9V reg ~ 2.2V
= 0.5 + grounded inputs
V for 3.3V reg ~ 3.7V
V for 1.1V reg ~ 1.5V
VLVDS = 1.9V
Need 3v3 plus 1v1 and 1v9 for the main ADC
Rbot = Rtop/(Vout-1) =100k/(1.5-1) = 200k
Rbot = Rtop/(Vout-1) =100k/(3.7-1) = ~37k
2A max current linear regs with 180mV dropout at 2A
Rbot = Rtop/(Vout-1) =100k/(2.2-1) = ~83k
3A max current buck converters take in 5V and put out voltages for linear reg that follows
Enable after Power Good 1.9V
