drandyhaas/HaasoscopePro/adc board/Kicad/Power_-_Amps.kicad_sch

## KiCad design adc board/Kicad/Power_-_Amps.kicad_sch (2025-04-30)

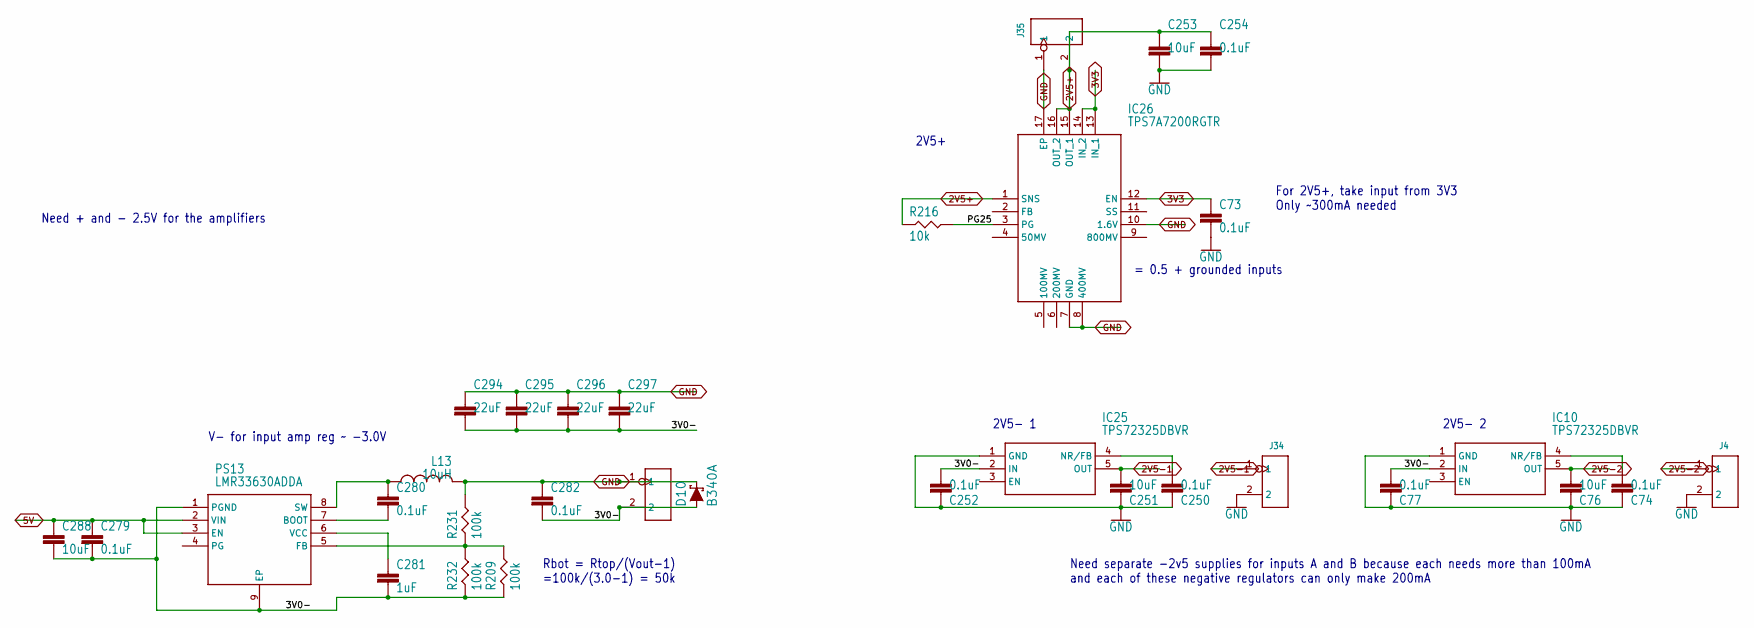
[picture p19: schematic Power_-_Amps.kicad_sch]

Parts:
C73, C74, C77, C250, C252, C254, C279, C280, C282: 0.1uF; RESC0402_N
C76, C251, C253, C288: 10uF; RESC0805_N
C281: 1uF; RESC0402_N
C294, C295, C296, C297: 22uF; RESC0805_N
D10: B340A; SMA-DIODE; LCSC C64982
IC10, IC25: TPS72325DBVR; SOT95P280X145-5N
IC26: TPS7A7200RGTR; QFN50P300X300X100-17N
J4, J34, J35, J44: 2p-2.54; H2-2.54
L13: 10uH; CDRH125; LCSC C339970
PS13: LMR33630ADDA; SOIC127P600X170-9N; LCSC C841384
R209, R231, R232: 100k; RES-0402
R216: 10k; RES-0402

Connections:
2V5+: C253.1, C254.1, IC26.1 (SNS), IC26.15 (OUT_1), IC26.16 (OUT_2), J35.2, R216.P$1
2V5-1: C251.1, IC25.5 (OUT), J34.1
2V5-2: C76.1, IC10.5 (OUT), J4.1
3V0-: C77.1, C252.1, C279.2, C281.2, C282.2, C288.2, C294.2, C295.2, C296.2, C297.2, D10.A, IC10.2 (IN), IC25.2 (IN), J44.2, PS13.1 (PGND), PS13.9 (EP), R209.P$1, R232.P$1
3V3: C73.1, IC26.12 (EN), IC26.13 (IN_1), IC26.14 (IN_2)
5V: C279.1, C288.1, PS13.2 (VIN), PS13.3 (EN)
GND: C73.2, C74.2, C76.2, C77.2, C250.2, C251.2, C252.2, C253.2, C254.2, C282.1, C294.1, C295.1, C296.1, C297.1, D10.C, IC10.1 (GND), IC25.1 (GND), IC26.7 (GND), IC26.8 (400MV), IC26.10 (1.6V), IC26.17 (EP), J4.2, J34.2, J35.1, J44.1, L13.2, R231.P$2
unnamed: C74.1, IC10.4 (NR/FB)
unnamed: C250.1, IC25.4 (NR/FB)
unnamed: C280.1, L13.1, PS13.8 (SW)
unnamed: C280.2, PS13.7 (BOOT)
unnamed: C281.1, PS13.6 (VCC)
unnamed: PS13.5 (FB), R209.P$2, R231.P$1, R232.P$2
PG25: IC26.3 (PG), R216.P$2

Notes on the sheet:
V- for input amp reg ~ -3.0V
2V5+
2V5- 1
2V5- 2
For 2V5+, take input from 3V3 Only ~300mA needed
= 0.5 + grounded inputs
Need separate -2v5 supplies for inputs A and B because each needs more than 100mA and each of these negative regulators can only make 200mA
Rbot = Rtop/(Vout-1) =100k/(3.0-1) = 50k
Need + and - 2.5V for the amplifiers
