drandyhaas/HaasoscopePro/adc board/Kicad/Power_-_FPGA.kicad_sch

## KiCad design adc board/Kicad/Power_-_FPGA.kicad_sch (2025-04-30)

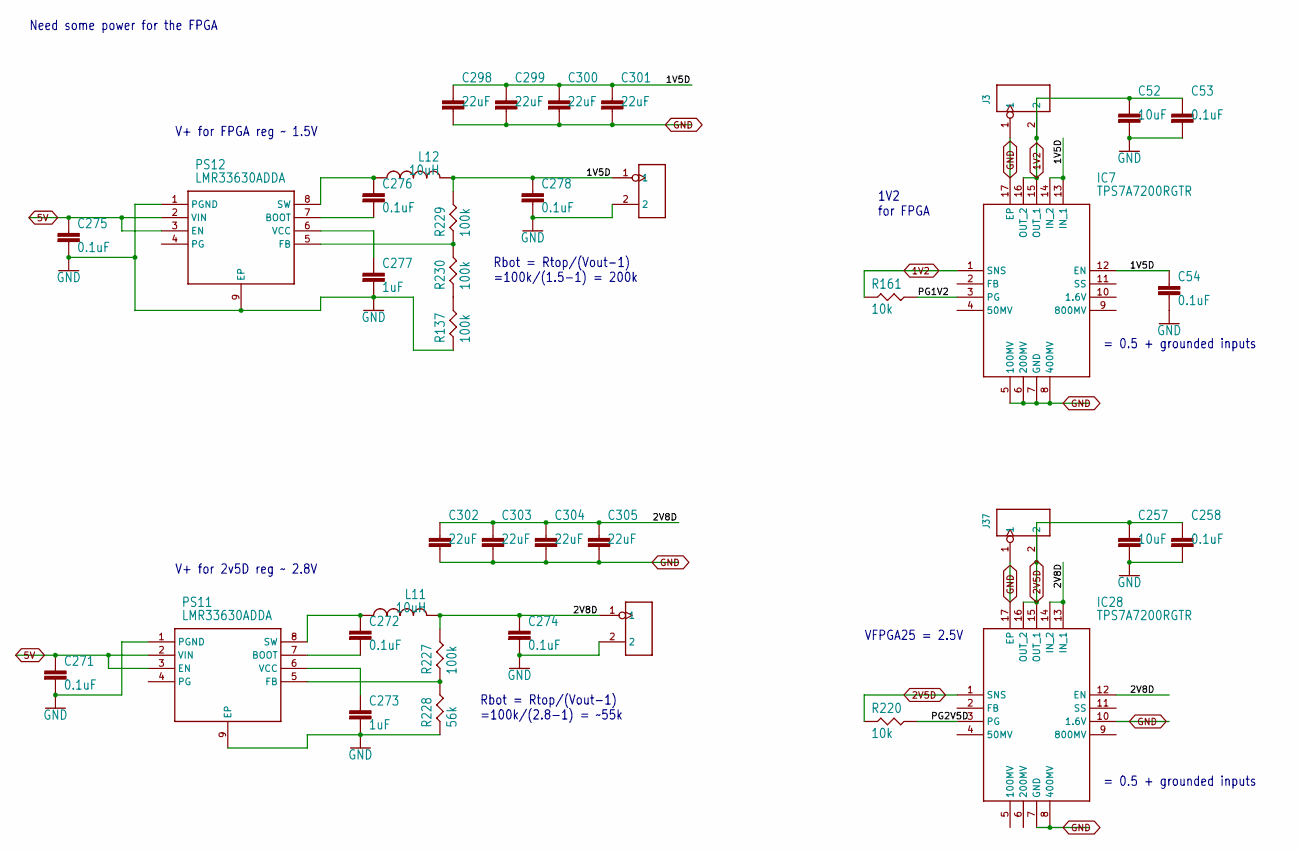
[picture p20: schematic Power_-_FPGA.kicad_sch]

Parts:
C52, C257: 10uF; RESC0805_N
C53, C54, C258, C271, C272, C274, C275, C276, C278: 0.1uF; RESC0402_N
C273, C277: 1uF; RESC0402_N
C298, C299, C300, C301, C302, C303, C304, C305: 22uF; RESC0805_N
IC7, IC28: TPS7A7200RGTR; QFN50P300X300X100-17N
J3, J37, J42, J43: 2p-2.54; H2-2.54
L11, L12: 10uH; CDRH125; LCSC C339970
PS11, PS12: LMR33630ADDA; SOIC127P600X170-9N; LCSC C841384
R137, R227, R229, R230: 100k; RES-0402
R161, R220: 10k; RES-0402
R228: 56k; RES-0402

Connections:
1V2: C52.1, C53.1, IC7.1 (SNS), IC7.15 (OUT_1), IC7.16 (OUT_2), J3.2, R161.P$1
1V5D: C54.1, C278.1, C298.1, C299.1, C300.1, C301.1, IC7.12 (EN), IC7.13 (IN_1), IC7.14 (IN_2), J43.1, L12.2, R229.P$2
2V5D: C257.1, C258.1, IC28.1 (SNS), IC28.15 (OUT_1), IC28.16 (OUT_2), J37.2, R220.P$1
2V8D: C274.1, C302.1, C303.1, C304.1, C305.1, IC28.12 (EN), IC28.13 (IN_1), IC28.14 (IN_2), J42.1, L11.2, R227.P$2
5V: C271.1, C275.1, PS11.2 (VIN), PS11.3 (EN), PS12.2 (VIN), PS12.3 (EN)
GND: C52.2, C53.2, C54.2, C257.2, C258.2, C271.2, C273.2, C274.2, C275.2, C277.2, C278.2, C298.2, C299.2, C300.2, C301.2, C302.2, C303.2, C304.2, C305.2, IC7.5 (100MV), IC7.6 (200MV), IC7.7 (GND), IC7.8 (400MV), IC7.17 (EP), IC28.7 (GND), IC28.8 (400MV), IC28.10 (1.6V), IC28.17 (EP), J3.1, J37.1, J42.2, J43.2, PS11.1 (PGND), PS11.9 (EP), PS12.1 (PGND), PS12.9 (EP), R137.P$1, R228.P$1
unnamed: C272.1, L11.1, PS11.8 (SW)
unnamed: C272.2, PS11.7 (BOOT)
unnamed: C273.1, PS11.6 (VCC)
unnamed: C276.1, L12.1, PS12.8 (SW)
unnamed: C276.2, PS12.7 (BOOT)
unnamed: C277.1, PS12.6 (VCC)
unnamed: PS11.5 (FB), R227.P$1, R228.P$2
unnamed: PS12.5 (FB), R229.P$1, R230.P$2
unnamed: R137.P$2, R230.P$1
PG1V2: IC7.3 (PG), R161.P$2
PG2V5D: IC28.3 (PG), R220.P$2

Notes on the sheet:
VFPGA25 = 2.5V
V+ for FPGA reg ~ 1.5V
Rbot = Rtop/(Vout-1) =100k/(1.5-1) = 200k
= 0.5 + grounded inputs
1V2 for FPGA
Rbot = Rtop/(Vout-1) =100k/(2.8-1) = ~55k
V+ for 2v5D reg ~ 2.8V
Need some power for the FPGA
