drandyhaas/HaasoscopePro/adc board/Kicad/Power_filters.kicad_sch

## KiCad design adc board/Kicad/Power_filters.kicad_sch (2025-04-30)

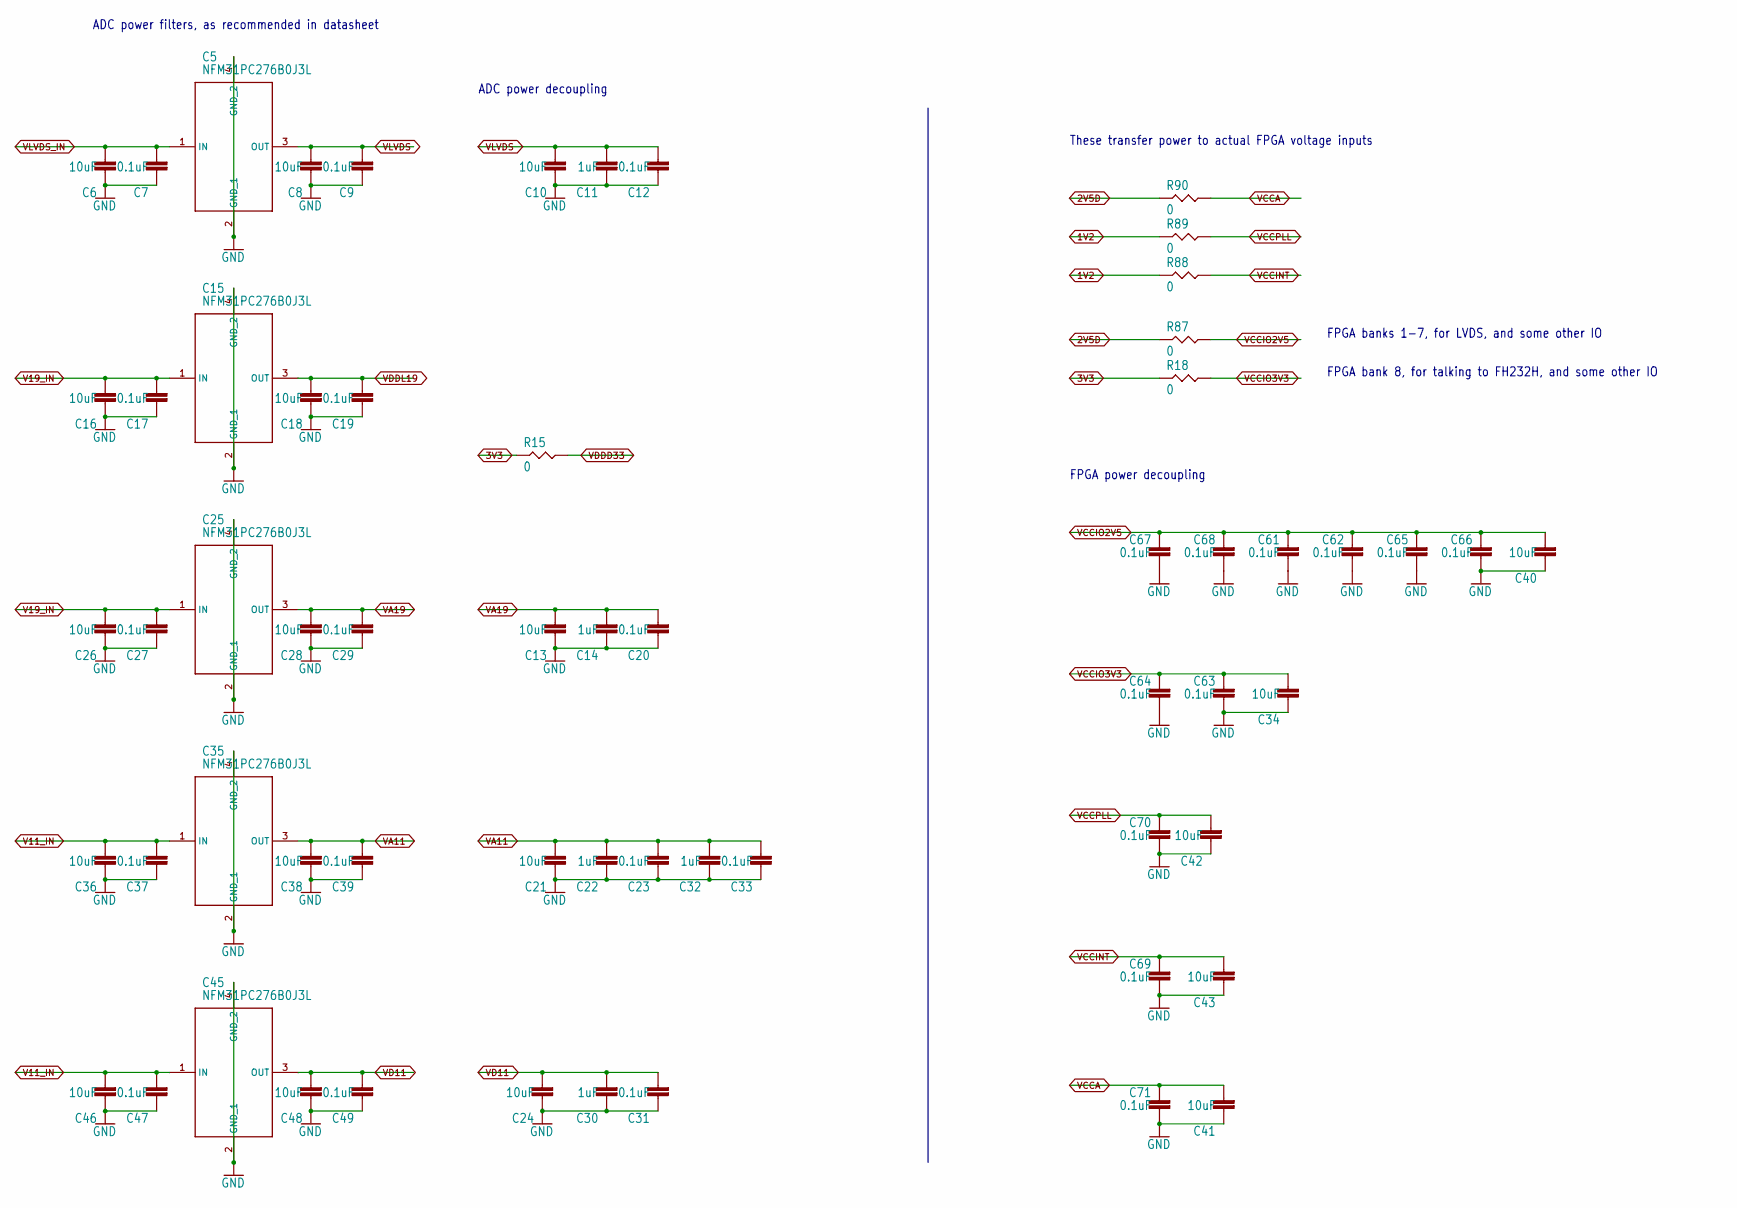
[picture p21: schematic Power_filters.kicad_sch]

Parts:
C5, C15, C25, C35, C45: NFM31PC276B0J3L; NFM31HK103R1H3L
C6, C8, C10, C13, C16, C18, C21, C24, C26, C28, C34, C36, C38, C40, C41, C42, C43, C46, C48: 10uF; RESC0805_N
C7, C9, C12, C17, C19, C20, C23, C27, C29, C31, C33, C37, C39, C47, C49, C61, C62, C63, C64, C65, C66, C67, C68, C69, C70, C71: 0.1uF; RESC0402_N
C11, C14, C22, C30, C32: 1uF; RESC0402_N
R15, R18, R87, R88, R89, R90: 0; RES-0402

Connections:
1V2: R88.P$1, R89.P$1
2V5D: R87.P$1, R90.P$1
3V3: R15.P$1, R18.P$1
GND: C5.2 (GND_1), C5.4 (GND_2), C6.1, C7.1, C8.1, C9.1, C10.1, C11.1, C12.1, C13.1, C14.1, C15.2 (GND_1), C15.4 (GND_2), C16.1, C17.1, C18.1, C19.1, C20.1, C21.1, C22.1, C23.1, C24.1, C25.2 (GND_1), C25.4 (GND_2), C26.1, C27.1, C28.1, C29.1, C30.1, C31.1, C32.1, C33.1, C34.1, C35.2 (GND_1), C35.4 (GND_2), C36.1, C37.1, C38.1, C39.1, C40.1, C41.1, C42.1, C43.1, C45.2 (GND_1), C45.4 (GND_2), C46.1, C47.1, C48.1, C49.1, C61.1, C62.1, C63.1, C64.1, C65.1, C66.1, C67.1, C68.1, C69.1, C70.1, C71.1
V11_IN: C35.1 (IN), C36.2, C37.2, C45.1 (IN), C46.2, C47.2
V19_IN: C15.1 (IN), C16.2, C17.2, C25.1 (IN), C26.2, C27.2
VA11: C21.2, C22.2, C23.2, C32.2, C33.2, C35.3 (OUT), C38.2, C39.2
VA19: C13.2, C14.2, C20.2, C25.3 (OUT), C28.2, C29.2
VCCA: C41.2, C71.2, R90.P$2
VCCINT: C43.2, C69.2, R88.P$2
VCCIO2V5: C40.2, C61.2, C62.2, C65.2, C66.2, C67.2, C68.2, R87.P$2
VCCIO3V3: C34.2, C63.2, C64.2, R18.P$2
VCCPLL: C42.2, C70.2, R89.P$2
VD11: C24.2, C30.2, C31.2, C45.3 (OUT), C48.2, C49.2
VDDD33: R15.P$2
VDDL19: C15.3 (OUT), C18.2, C19.2
VLVDS: C5.3 (OUT), C8.2, C9.2, C10.2, C11.2, C12.2
VLVDS_IN: C5.1 (IN), C6.2, C7.2

Notes on the sheet:
ADC power decoupling
FPGA power decoupling
These transfer power to actual FPGA voltage inputs
FPGA banks 1-7, for LVDS, and some other IO
ADC power filters, as recommended in datasheet
FPGA bank 8, for talking to FH232H, and some other IO
