drandyhaas/HaasoscopePro/adc board/Kicad/Preinput_1.kicad_sch

## KiCad design adc board/Kicad/Preinput_1.kicad_sch (2025-04-30)

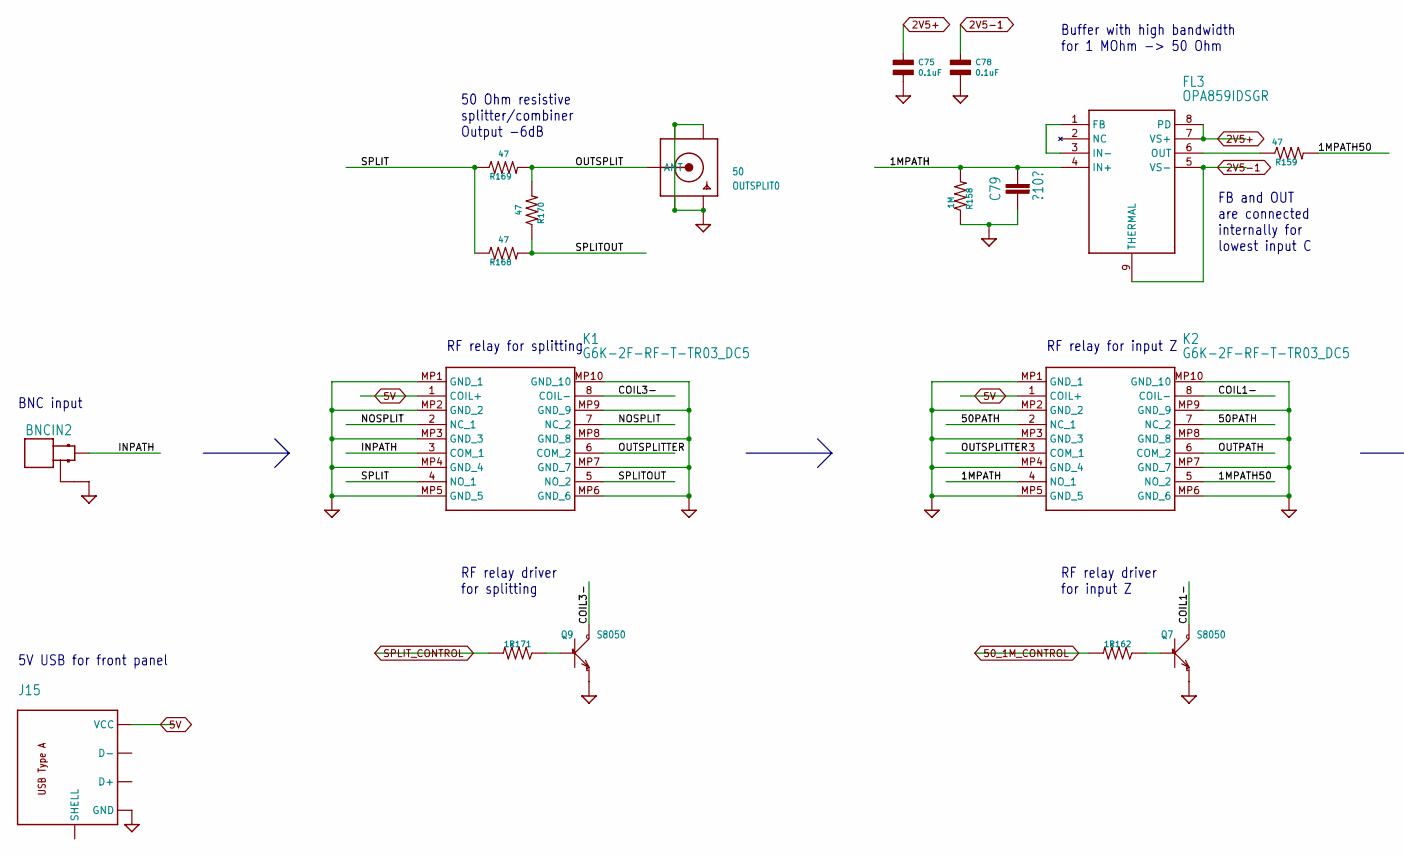
[picture p22: schematic Preinput_1.kicad_sch, part in row 1, column 1]

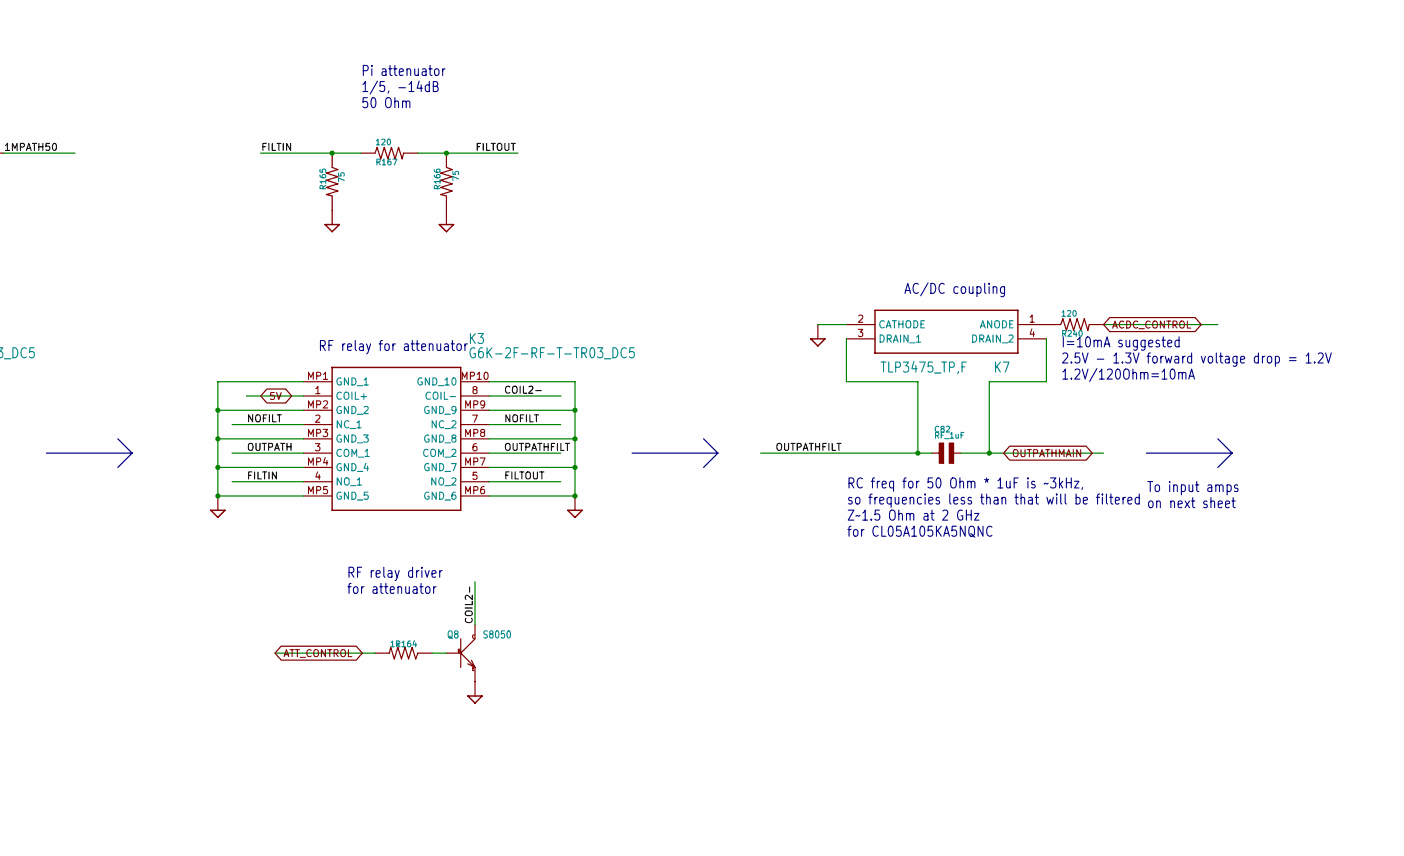
[picture p23: schematic Preinput_1.kicad_sch, part in row 1, column 2]

Parts:
BNCIN2: MOLEX_BNC_73100-0105; MOLEX-BNC-73100-0105; MPN 73100-0105
C75, C78: 0.1uF; C0402
C79: ?10?; C0805
C82: RF_1uF; C0402; LCSC C52923
FL3: OPA859IDSGR; SON50P200X200X80-9N
J15: test1; USB-2.0-A-THT-RA-TE_AMP-292303-1
K1, K2, K3: G6K-2F-RF-T-TR03_DC5; G6K2FRFTTR03DC5
K7: TLP3475_TP,F; TLP3475TPF; MANUFACTURER_PART_NUMBER TLP3475; MOUSER_PART_NUMBER 757-TLP3475
OUTSPLIT0: 50; SMA_EDGELAUNCH
Q7, Q8, Q9: S8050; SOT-23; LCSC C7420370
R158: 1M; R0402
R159, R168, R169, R170: 47; R0402
R162, R164, R171: 1k; R0402
R165, R166: 75; R0402
R167, R240: 120; R0402

Connections:
1MPATH: C79.2, FL3.4 (IN+), K2.4 (NO_1), R158.P$2
1MPATH50: K2.5 (NO_2), R159.P$2
2V5+: C75.P$1, FL3.7 (VS+), FL3.8 (PD)
2V5-1: C78.P$1, FL3.5 (VS-), FL3.9 (THERMAL)
5V: J15.P$1 (VCC), K1.1 (COIL+), K2.1 (COIL+), K3.1 (COIL+)
50PATH: K2.2 (NC_1), K2.7 (NC_2)
50_1M_CONTROL: R162.P$2
ACDC_CONTROL: R240.P$2
ATT_CONTROL: R164.P$2
COIL1-: K2.8 (COIL-), Q7.3 (C)
COIL2-: K3.8 (COIL-), Q8.3 (C)
COIL3-: K1.8 (COIL-), Q9.3 (C)
FILTIN: K3.4 (NO_1), R165.P$1, R167.P$1
FILTOUT: K3.5 (NO_2), R166.P$1, R167.P$2
GND: BNCIN2.GND1 (GND), BNCIN2.GND2 (GND), C75.P$2, C78.P$2, C79.1, J15.P$4 (GND), K1.MP1 (GND_1), K1.MP2 (GND_2), K1.MP3 (GND_3), K1.MP4 (GND_4), K1.MP5 (GND_5), K1.MP6 (GND_6), K1.MP7 (GND_7), K1.MP8 (GND_8), K1.MP9 (GND_9), K1.MP10 (GND_10), K2.MP1 (GND_1), K2.MP2 (GND_2), K2.MP3 (GND_3), K2.MP4 (GND_4), K2.MP5 (GND_5), K2.MP6 (GND_6), K2.MP7 (GND_7), K2.MP8 (GND_8), K2.MP9 (GND_9), K2.MP10 (GND_10), K3.MP1 (GND_1), K3.MP2 (GND_2), K3.MP3 (GND_3), K3.MP4 (GND_4), K3.MP5 (GND_5), K3.MP6 (GND_6), K3.MP7 (GND_7), K3.MP8 (GND_8), K3.MP9 (GND_9), K3.MP10 (GND_10), K7.2 (CATHODE), OUTSPLIT0.GND@1 (GND4), OUTSPLIT0.GND@2 (GND3), OUTSPLIT0.GND@3 (GND2), OUTSPLIT0.GND@4 (GND1), Q7.2 (E), Q8.2 (E), Q9.2 (E), R158.P$1, R165.P$2, R166.P$2
INPATH: BNCIN2.SIGNAL, K1.3 (COM_1)
NOFILT: K3.2 (NC_1), K3.7 (NC_2)
NOSPLIT: K1.2 (NC_1), K1.7 (NC_2)
unnamed: FL3.1 (FB), FL3.3 (IN-)
unnamed: FL3.6 (OUT), R159.P$1
unnamed: J15.S$1 (SHELL), J15.S$2 (SHELL)
unnamed: K7.1 (ANODE), R240.P$1
unnamed: Q7.1 (B), R162.P$1
unnamed: Q8.1 (B), R164.P$1
unnamed: Q9.1 (B), R171.P$1
OUTPATH: K2.6 (COM_2), K3.3 (COM_1)
OUTPATHFILT: C82.P$1, K3.6 (COM_2), K7.3 (DRAIN_1)
OUTPATHMAIN: C82.P$2, K7.4 (DRAIN_2)
OUTSPLIT: OUTSPLIT0.P (ANT), R169.P$2, R170.P$2
OUTSPLITTER: K1.6 (COM_2), K2.3 (COM_1)
SPLIT: K1.4 (NO_1), R168.P$1, R169.P$1
SPLITOUT: K1.5 (NO_2), R168.P$2, R170.P$1
SPLIT_CONTROL: R171.P$2

Notes on the sheet:
I=10mA suggested 2.5V - 1.3V forward voltage drop = 1.2V 1.2V/120Ohm=10mA
FB and OUT are connected internally for lowest input C
RF relay for input Z
BNC input
RF relay for attenuator
To input amps on next sheet
RC freq for 50 Ohm * 1uF is ~3kHz, so frequencies less than that will be filtered Z~1.5 Ohm at 2 GHz for CL05A105KA5NQNC
RF relay driver for input Z
RF relay driver for splitting
50 Ohm resistive splitter/combiner Output -6dB
RF relay driver for attenuator
Buffer with high bandwidth for 1 MOhm -> 50 Ohm
RF relay for splitting
Pi attenuator 1/5, -14dB 50 Ohm
AC/DC coupling
5V USB for front panel
