drandyhaas/HaasoscopePro/adc board/Kicad/Preinput_2.kicad_sch

## KiCad design adc board/Kicad/Preinput_2.kicad_sch (2025-04-30)

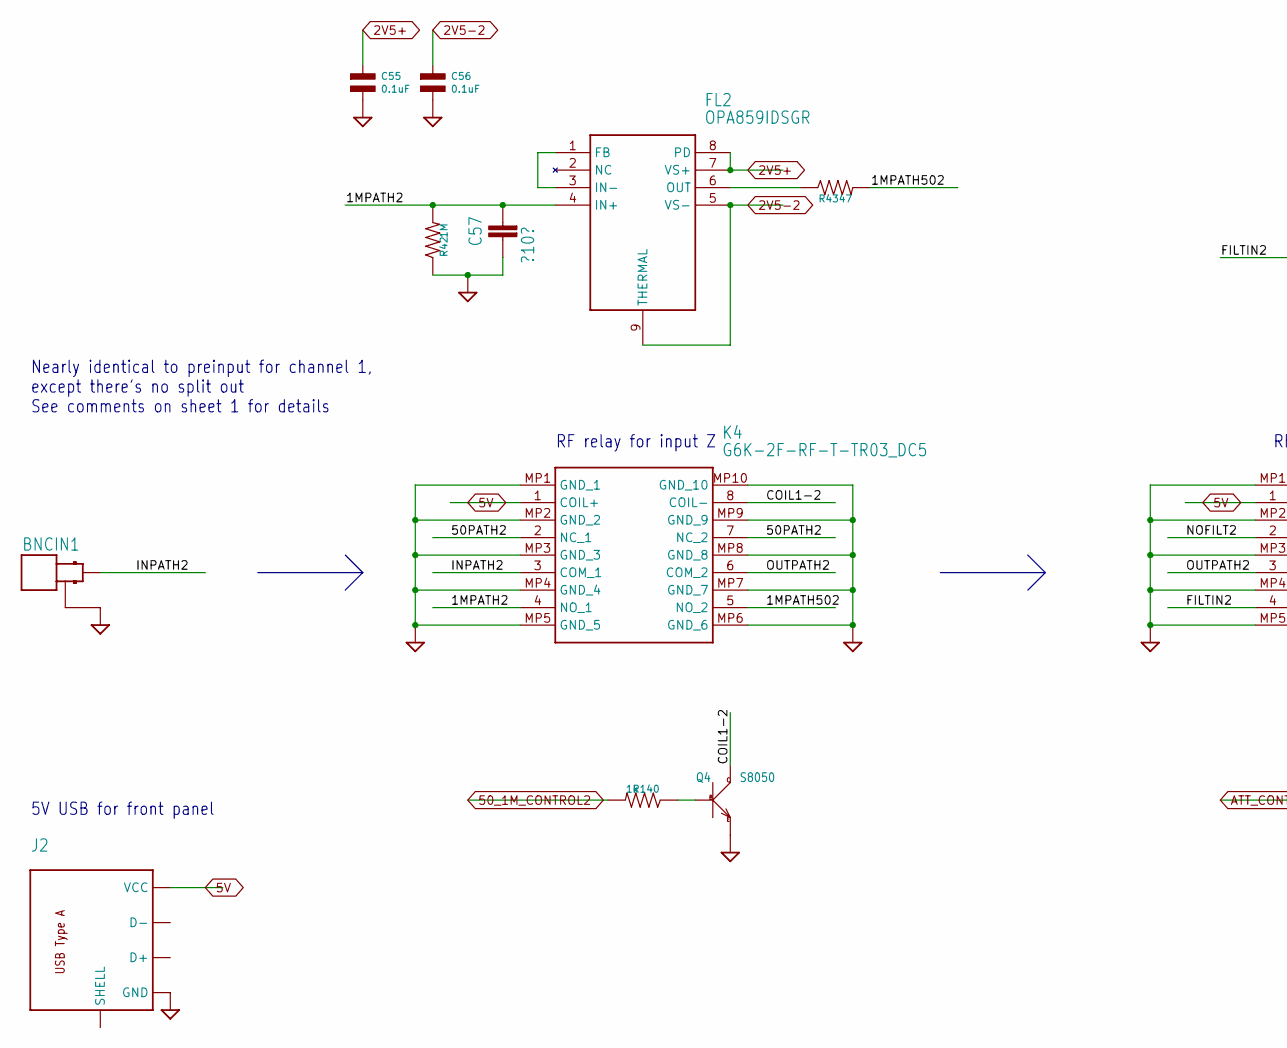
[picture p24: schematic Preinput_2.kicad_sch, part in row 1, column 1]

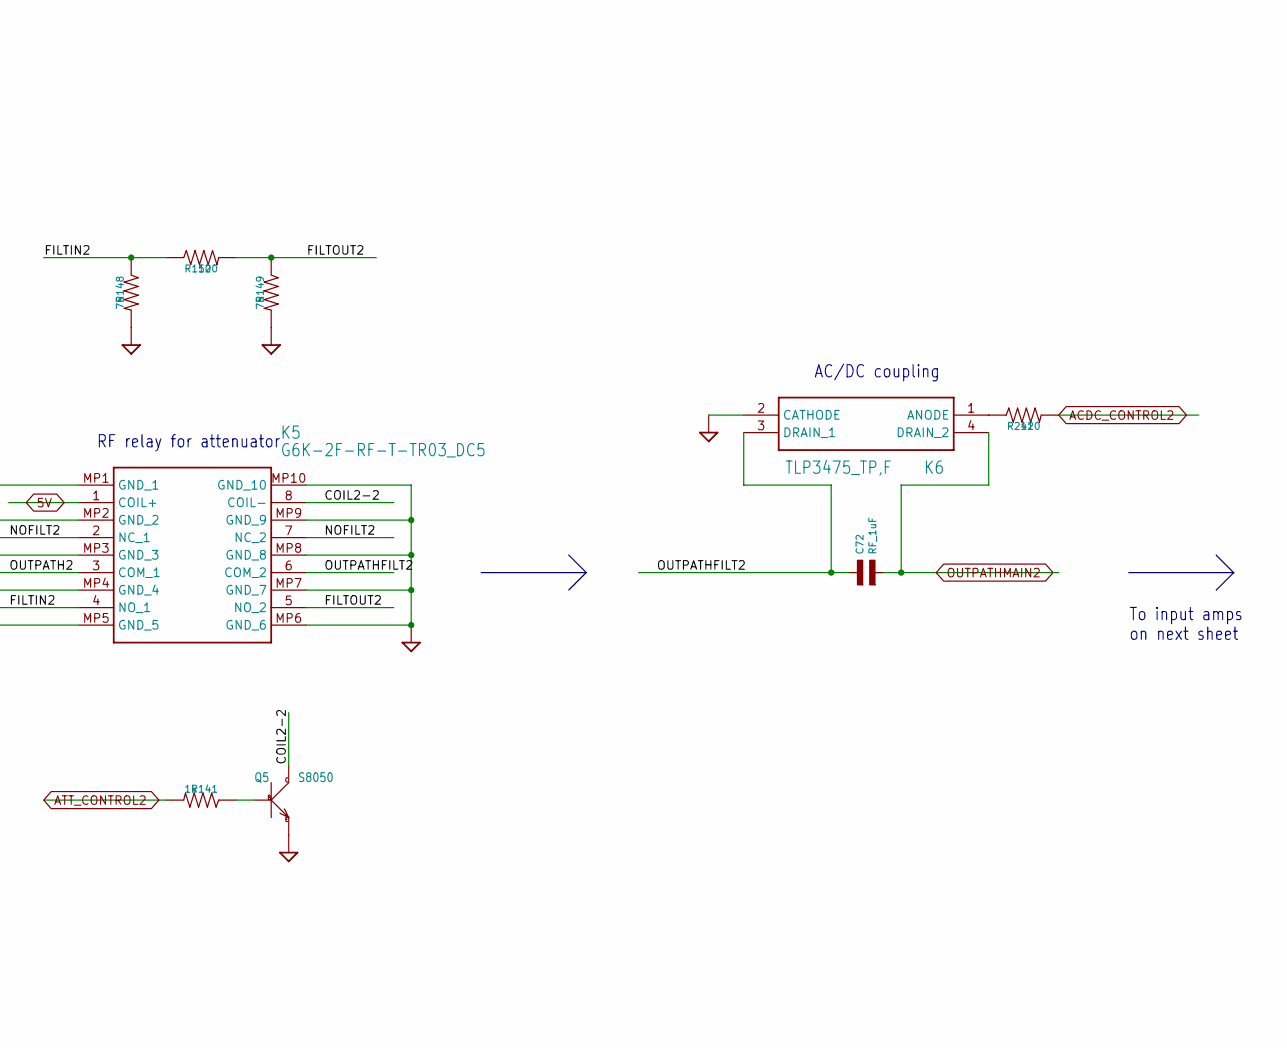
[picture p25: schematic Preinput_2.kicad_sch, part in row 1, column 2]

Parts:
BNCIN1: MOLEX_BNC_73100-0105; MOLEX-BNC-73100-0105; MPN 73100-0105
C55, C56: 0.1uF; C0402
C57: ?10?; C0805
C72: RF_1uF; C0402; LCSC C52923
FL2: OPA859IDSGR; SON50P200X200X80-9N
J2: test1; USB-2.0-A-THT-RA-TE_AMP-292303-1
K4, K5: G6K-2F-RF-T-TR03_DC5; G6K2FRFTTR03DC5
K6: TLP3475_TP,F; TLP3475TPF; MANUFACTURER_PART_NUMBER TLP3475; MOUSER_PART_NUMBER 757-TLP3475
Q4, Q5: S8050; SOT-23; LCSC C7420370
R42: 1M; R0402
R43: 47; R0402
R140, R141: 1k; R0402
R148, R149: 75; R0402
R150, R241: 120; R0402

Connections:
1MPATH2: C57.2, FL2.4 (IN+), K4.4 (NO_1), R42.P$2
1MPATH502: K4.5 (NO_2), R43.P$2
2V5+: C55.P$1, FL2.7 (VS+), FL2.8 (PD)
2V5-2: C56.P$1, FL2.5 (VS-), FL2.9 (THERMAL)
5V: J2.P$1 (VCC), K4.1 (COIL+), K5.1 (COIL+)
50PATH2: K4.2 (NC_1), K4.7 (NC_2)
50_1M_CONTROL2: R140.P$2
ACDC_CONTROL2: R241.P$2
ATT_CONTROL2: R141.P$2
COIL1-2: K4.8 (COIL-), Q4.3 (C)
COIL2-2: K5.8 (COIL-), Q5.3 (C)
FILTIN2: K5.4 (NO_1), R148.P$1, R150.P$1
FILTOUT2: K5.5 (NO_2), R149.P$1, R150.P$2
GND: BNCIN1.GND1 (GND), BNCIN1.GND2 (GND), C55.P$2, C56.P$2, C57.1, J2.P$4 (GND), K4.MP1 (GND_1), K4.MP2 (GND_2), K4.MP3 (GND_3), K4.MP4 (GND_4), K4.MP5 (GND_5), K4.MP6 (GND_6), K4.MP7 (GND_7), K4.MP8 (GND_8), K4.MP9 (GND_9), K4.MP10 (GND_10), K5.MP1 (GND_1), K5.MP2 (GND_2), K5.MP3 (GND_3), K5.MP4 (GND_4), K5.MP5 (GND_5), K5.MP6 (GND_6), K5.MP7 (GND_7), K5.MP8 (GND_8), K5.MP9 (GND_9), K5.MP10 (GND_10), K6.2 (CATHODE), Q4.2 (E), Q5.2 (E), R42.P$1, R148.P$2, R149.P$2
INPATH2: BNCIN1.SIGNAL, K4.3 (COM_1)
NOFILT2: K5.2 (NC_1), K5.7 (NC_2)
unnamed: FL2.1 (FB), FL2.3 (IN-)
unnamed: FL2.6 (OUT), R43.P$1
unnamed: J2.S$1 (SHELL), J2.S$2 (SHELL)
unnamed: K6.1 (ANODE), R241.P$1
unnamed: Q4.1 (B), R140.P$1
unnamed: Q5.1 (B), R141.P$1
OUTPATH2: K4.6 (COM_2), K5.3 (COM_1)
OUTPATHFILT2: C72.P$1, K5.6 (COM_2), K6.3 (DRAIN_1)
OUTPATHMAIN2: C72.P$2, K6.4 (DRAIN_2)

Notes on the sheet:
RF relay for input Z
5V USB for front panel
Nearly identical to preinput for channel 1, except there's no split out See comments on sheet 1 for details
AC/DC coupling
RF relay for attenuator
To input amps on next sheet
