drandyhaas/HaasoscopePro/adc board/Kicad/Temp_mon.kicad_sch

## KiCad design adc board/Kicad/Temp_mon.kicad_sch (2025-04-30)

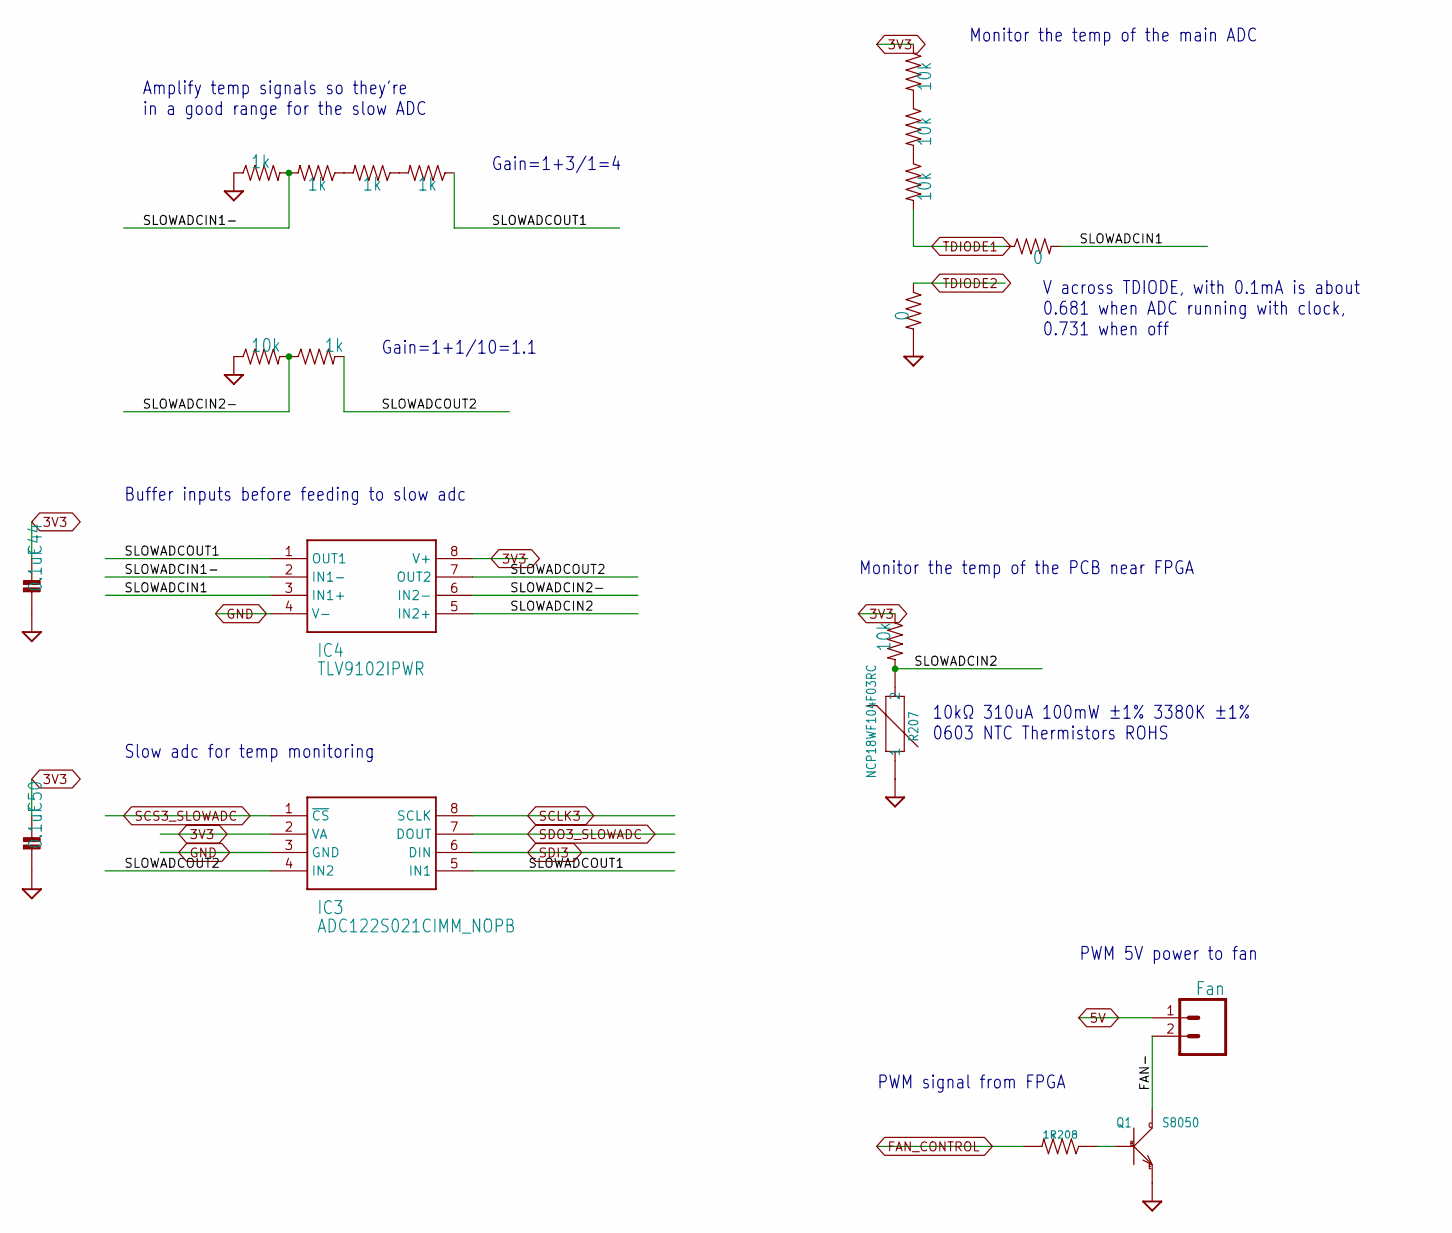
[picture p26: schematic Temp_mon.kicad_sch]

Parts:
C44, C50: 0.1uF; 0402_CAP
IC3: ADC122S021CIMM_NOPB; SOP65P490X110-8N
IC4: TLV9102IPWR; SOP65P640X120-8N
JST_FAN0: Fan; 1X02
Q1: S8050; SOT-23; LCSC C7420370
R122, R124, R126, R202, R203: 1k; 0402_RES
R125, R127, R130, R186, R198: 10k; 0402_RES
R128, R129: 0; 0402_RES
R207: NCP18WF104F03RC; R0603; MPN NCP18XH103F03RB; LCSC C13564
R208: 1k; R0402

Connections:
3V3: C44.1, C50.1, IC3.2 (VA), IC4.8 (V+), R127.1, R130.1
5V: JST_FAN0.1
FAN-: JST_FAN0.2, Q1.3 (C)
FAN_CONTROL: R208.P$2
GND: C44.2, C50.2, IC3.3 (GND), IC4.4 (V-), Q1.2 (E), R124.1, R125.1, R128.2, R207.1
unnamed: Q1.1 (B), R208.P$1
unnamed: R122.2, R202.1
unnamed: R127.2, R186.1
unnamed: R186.2, R198.1
unnamed: R202.2, R203.1
SCLK3: IC3.8 (SCLK)
SCS3_SLOWADC: IC3.1 (~CS)
SDI3: IC3.6 (DIN)
SDO3_SLOWADC: IC3.7 (DOUT)
SLOWADCIN1: IC4.3 (IN1+), R129.2
SLOWADCIN1-: IC4.2 (IN1-), R124.2, R203.2
SLOWADCIN2: IC4.5 (IN2+), R130.2, R207.2
SLOWADCIN2-: IC4.6 (IN2-), R125.2, R126.1
SLOWADCOUT1: IC3.5 (IN1), IC4.1 (OUT1), R122.1
SLOWADCOUT2: IC3.4 (IN2), IC4.7 (OUT2), R126.2
TDIODE1: R129.1, R198.2
TDIODE2: R128.1

Notes on the sheet:
V across TDIODE, with 0.1mA is about 0.681 when ADC running with clock, 0.731 when off
Slow adc for temp monitoring
Monitor the temp of the PCB near FPGA
PWM signal from FPGA
Buffer inputs before feeding to slow adc
10kΩ 310uA 100mW ±1% 3380K ±1% 0603 NTC Thermistors ROHS
Monitor the temp of the main ADC
PWM 5V power to fan
Gain=1+3/1=4
Gain=1+1/10=1.1
Amplify temp signals so they're in a good range for the slow ADC
