drandyhaas/HaasoscopePro/adc board firmware/clkctrl/synthesis/clkctrl.v

// clkctrl.v

// Generated using ACDS version 23.1 993

`timescale 1 ps / 1 ps
module clkctrl (
		input  wire  inclk,  //  altclkctrl_input.inclk
		input  wire  ena,    //                  .ena
		output wire  outclk  // altclkctrl_output.outclk
	);

	clkctrl_altclkctrl_0 altclkctrl_0 (
		.inclk  (inclk),  //  altclkctrl_input.inclk
		.ena    (ena),    //                  .ena
		.outclk (outclk)  // altclkctrl_output.outclk
	);

endmodule
