drandyhaas/HaasoscopePro/adc board firmware/remoteupdate/remoteupdate_inst.v

	remoteupdate u0 (
		.busy        (<connected-to-busy>),        //        busy.busy
		.data_out    (<connected-to-data_out>),    //    data_out.data_out
		.param       (<connected-to-param>),       //       param.param
		.read_param  (<connected-to-read_param>),  //  read_param.read_param
		.reconfig    (<connected-to-reconfig>),    //    reconfig.reconfig
		.reset_timer (<connected-to-reset_timer>), // reset_timer.reset_timer
		.read_source (<connected-to-read_source>), // read_source.read_source
		.clock       (<connected-to-clock>),       //       clock.clk
		.reset       (<connected-to-reset>)        //       reset.reset
	);
